Stemfie3D/STEMFIE-file-repository/Beams/Angled/U-shaped Symmetric/Beam AGD USH SYM ESS (thumbnail).png

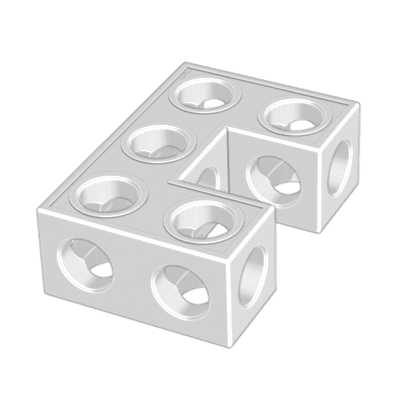
Beams/Angled/U-shaped Symmetric/Beam AGD USH SYM ESS (thumbnail).png
