Stemfie3D/STEMFIE-file-repository/Beams/Straight/Threaded Ends/Beam STR ERHRH DE ESS (thumbnail).png

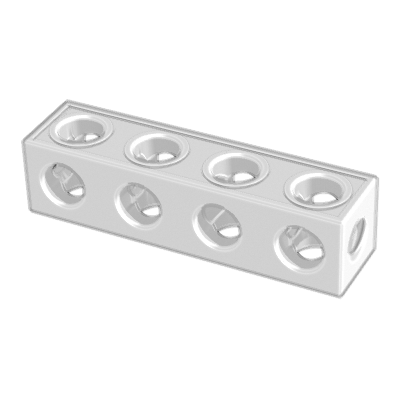
Beams/Straight/Threaded Ends/Beam STR ERHRH DE ESS (thumbnail).png
