Stemfie3D/STEMFIE-file-repository/Braces/Angled/90 Degrees Asymmetric/Brace AGD 90 ASYM ERR (thumbnail).png

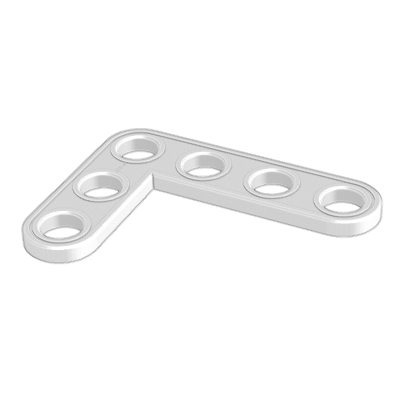
Braces/Angled/90 Degrees Asymmetric/Brace AGD 90 ASYM ERR (thumbnail).png
