Stemfie3D/STEMFIE-file-repository/Braces/Straight/Slotted Both Ends/Brace STR SLT BE SYM ERR (thumbnail).png

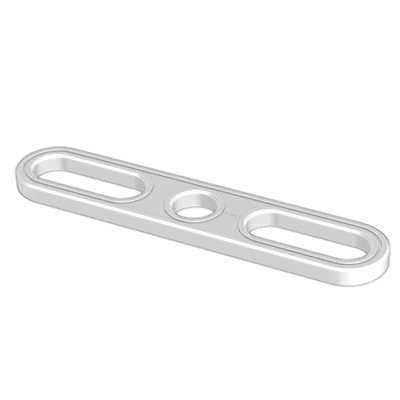
Braces/Straight/Slotted Both Ends/Brace STR SLT BE SYM ERR (thumbnail).png
