Stemfie3D/STEMFIE-file-repository/Braces/Straight/Slotted Sequential/Brace STR SLT SQT ERR (thumbnail).png

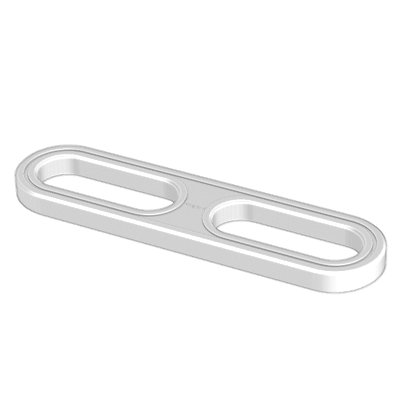
Braces/Straight/Slotted Sequential/Brace STR SLT SQT ERR (thumbnail).png
