Stemfie3D/STEMFIE-file-repository/Connectors/Beam Through-Hole/Connector BEM THR-H SFT (thumbnail).png

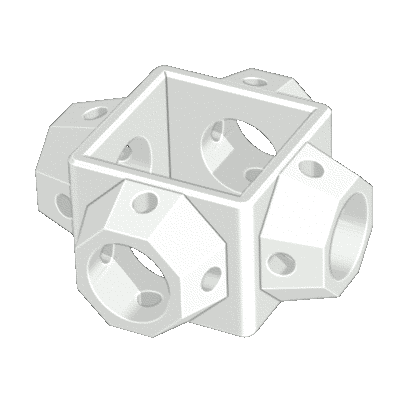
Connectors/Beam Through-Hole/Connector BEM THR-H SFT (thumbnail).png
