Stemfie3D/STEMFIE-file-repository/Fasteners/Nuts/Cam-locking/Open/Nut PH CL (thumbnail).png

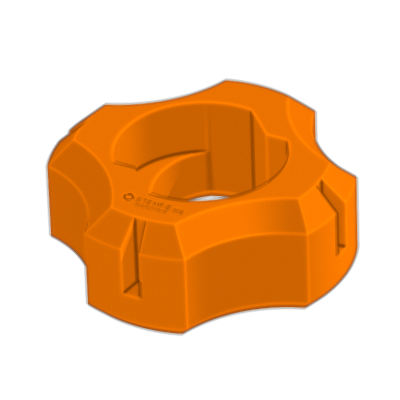
Fasteners/Nuts/Cam-locking/Open/Nut PH CL (thumbnail).png
