Stemfie3D/STEMFIE-file-repository/Fasteners/Nuts/Threaded/Open/Nut RH (thumbnail).png

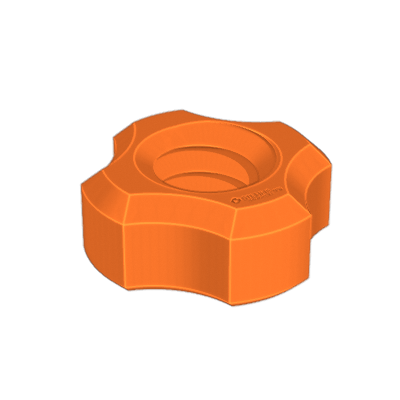
Fasteners/Nuts/Threaded/Open/Nut RH (thumbnail).png
