Stemfie3D/STEMFIE-file-repository/Fasteners/Screws/Fully Threaded STEMFIE Head/Screw SHD CRS STA FT RH (thumbnail).png

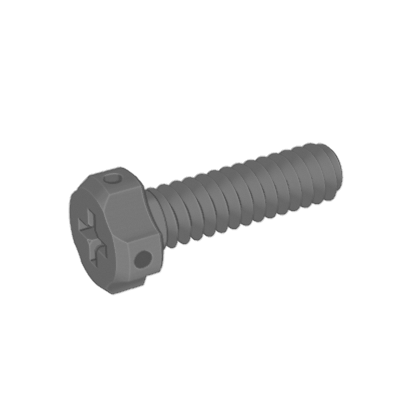
Fasteners/Screws/Fully Threaded STEMFIE Head/Screw SHD CRS STA FT RH (thumbnail).png
