Stemfie3D/STEMFIE-file-repository/Fasteners/Washers/Fixed/Washer FXD (thumbnail).png

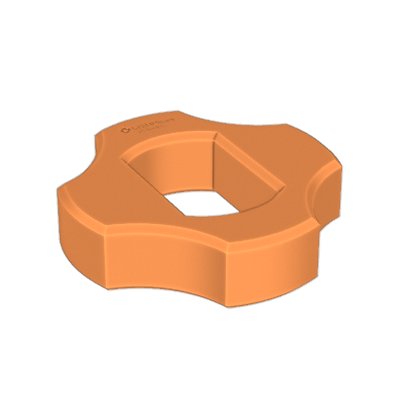
Fasteners/Washers/Fixed/Washer FXD (thumbnail).png
