Stemfie3D/STEMFIE-file-repository/Plates/3 - Triangular/Plate TRI (thumbnail).png

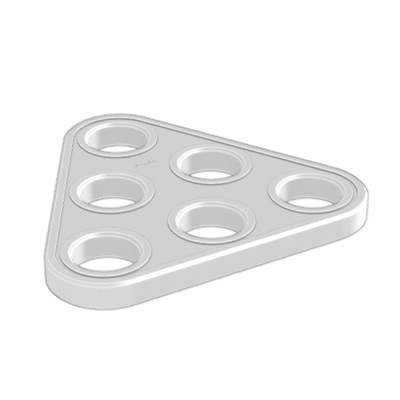
Plates/3 - Triangular/Plate TRI (thumbnail).png
