Stemfie3D/STEMFIE-file-repository/Plates/6 - Hexagonal/Plate HEX (thumbnail).png

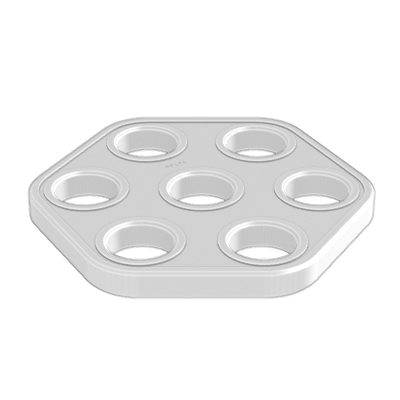
Plates/6 - Hexagonal/Plate HEX (thumbnail).png
