Stemfie3D/STEMFIE-file-repository/Springs/Rotor/Spring RTR (thumbnail).png

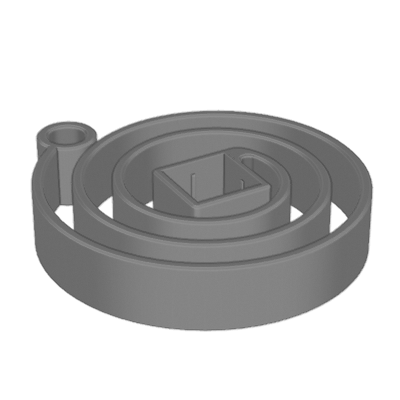
Springs/Rotor/Spring RTR (thumbnail).png
