Stemfie3D/STEMFIE-file-repository/Braces/Angled/90 Degrees Asymmetric/Brace AGD 90 ASYM ERR BU09x13x01x00.25 - SPN-BRC-1108 (stemfie.org).stl

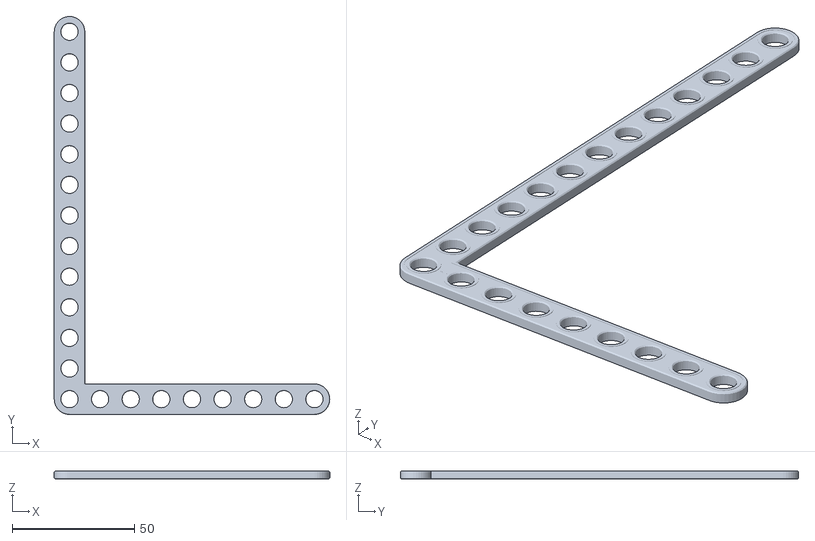
[picture p33: CAD file, 2023-08-30]
Braces/Angled/90 Degrees Asymmetric/Brace AGD 90 ASYM ERR BU09x13x01x00.25 - SPN-BRC-1108 (stemfie.org).stl
112.5 x 162.5 x 3.13
