Stemfie3D/STEMFIE-file-repository/Braces/Straight/Slotted Both Ends/Brace STR SLT BE SYM ERR BU20x01x00.25x09 - SPN-BRC-0372 (stemfie.org).stl

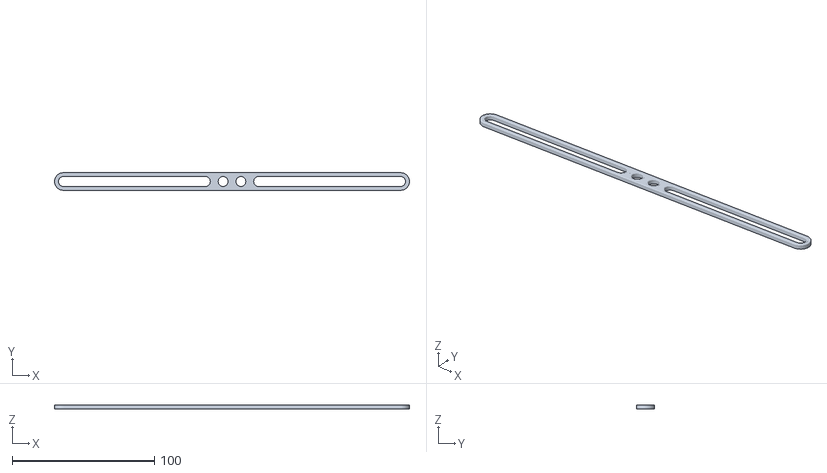
[picture p34: CAD file, 2021-05-27]
Braces/Straight/Slotted Both Ends/Brace STR SLT BE SYM ERR BU20x01x00.25x09 - SPN-BRC-0372 (stemfie.org).stl
250.0 x 12.5 x 3.13
