Stemfie3D/STEMFIE-file-repository/Braces/Straight/Slotted Centered/Brace STR SLT CNT ERR BU18x01x00.25x06 - SPN-BRC-0404 (stemfie.org).stl

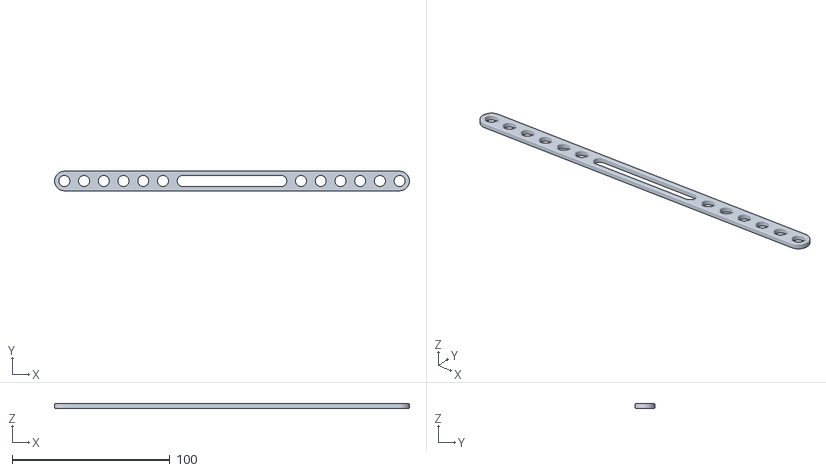
[picture p35: CAD file, 2021-05-27]
Braces/Straight/Slotted Centered/Brace STR SLT CNT ERR BU18x01x00.25x06 - SPN-BRC-0404 (stemfie.org).stl
225.0 x 12.5 x 3.12
