Stemfie3D/STEMFIE-file-repository/Braces/Straight/Slotted Full Length/Brace STR SLT FL ERR BU10x01x00.25 - SPN-BRC-0111 (stemfie.org).stl

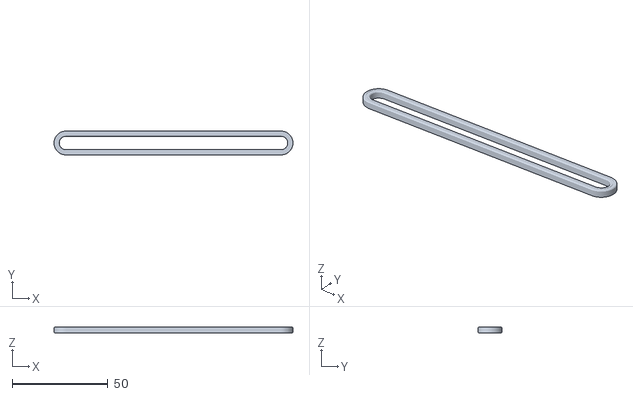
[picture p36: CAD file, 2021-05-27]
Braces/Straight/Slotted Full Length/Brace STR SLT FL ERR BU10x01x00.25 - SPN-BRC-0111 (stemfie.org).stl
125.0 x 12.5 x 3.13
