Stemfie3D/STEMFIE-file-repository/Braces/Straight/Slotted Sequential/Brace STR SLT SQT ERR BU04x01x00.25x02 - SPN-BRC-0419 (stemfie.org).stl

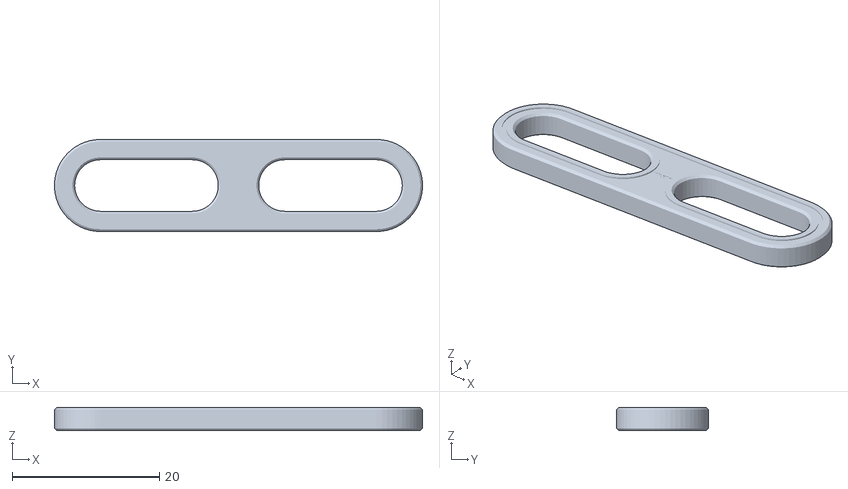
[picture p37: CAD file, 2022-02-20]
Braces/Straight/Slotted Sequential/Brace STR SLT SQT ERR BU04x01x00.25x02 - SPN-BRC-0419 (stemfie.org).stl
50.0 x 12.5 x 3.12
