Stemfie3D/STEMFIE-file-repository/Braces/Straight/Slotted Single End/Brace STR SLT SE ERR BU17x01x00.25x10 - SPN-BRC-0235 (stemfie.org).stl

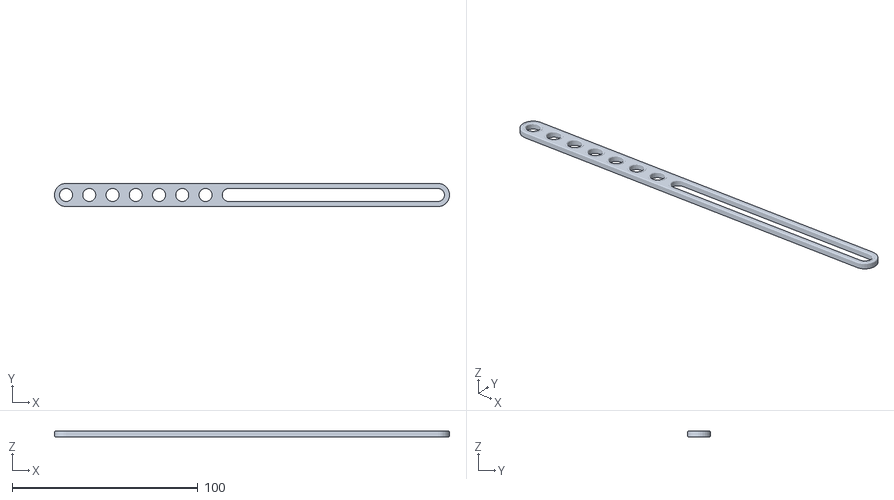
[picture p38: CAD file, 2021-05-27]
Braces/Straight/Slotted Single End/Brace STR SLT SE ERR BU17x01x00.25x10 - SPN-BRC-0235 (stemfie.org).stl
212.4 x 12.5 x 3.12
