Stemfie3D/STEMFIE-file-repository/Braces/Straight/Standard/Brace STR STD ERR BU27x01x00.25 - SPN-BRC-0026 (stemfie.org).stl

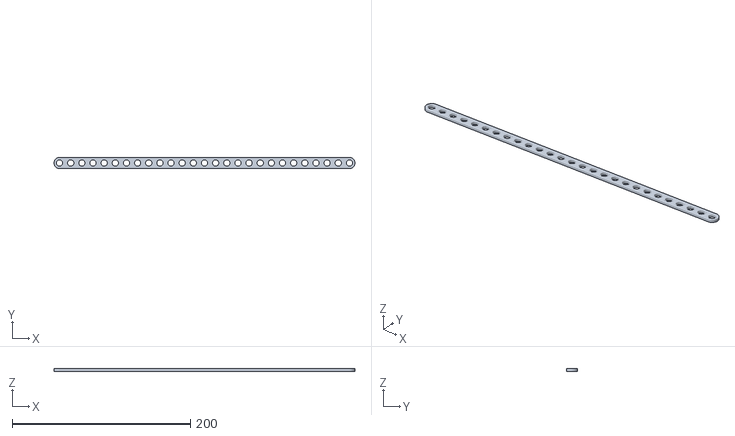
[picture p39: CAD file, 2021-05-27]
Braces/Straight/Standard/Brace STR STD ERR BU27x01x00.25 - SPN-BRC-0026 (stemfie.org).stl
337.5 x 12.5 x 3.12
