Stemfie3D/STEMFIE-file-repository/Braces/Straight/Standard/Build Plates/Brace STR ERR BU07x01x00.25 - SPN-BRC-0006 (stemfie.org) 13x 3D-printing build plate.3mf

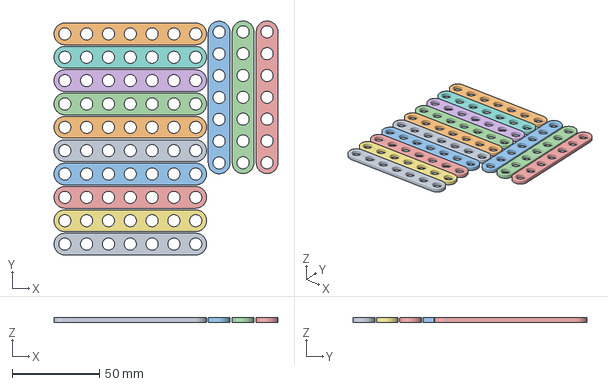
[picture p40: CAD file, 2021-05-27]
Braces/Straight/Standard/Build Plates/Brace STR ERR BU07x01x00.25 - SPN-BRC-0006 (stemfie.org) 13x 3D-printing build plate.3mf
128.3 x 134.1 x 3.12 mm
