Stemfie3D/STEMFIE-file-repository/Connectors/Beam Through-Hole/Connector BEM THR-H SFT 3W BU01x01x01x00.50 - SPN-CON-0004 (stemfie.org).stl

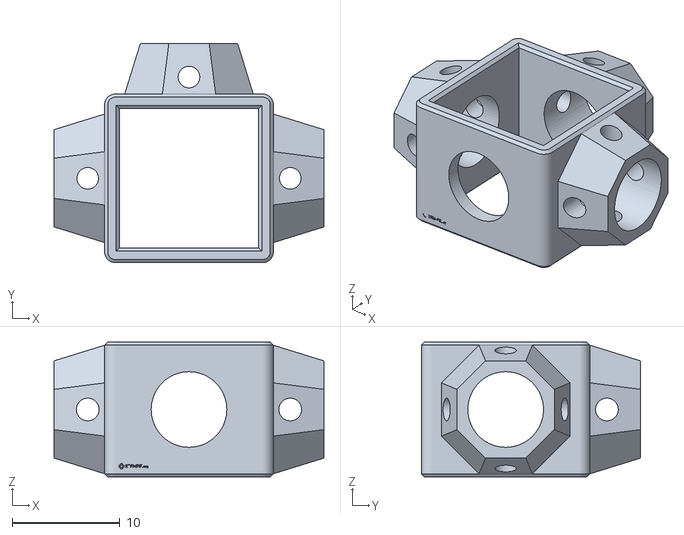
[picture p41: CAD file, 2021-05-27]
Connectors/Beam Through-Hole/Connector BEM THR-H SFT 3W BU01x01x01x00.50 - SPN-CON-0004 (stemfie.org).stl
25.0 x 20.3 x 12.5
