Stemfie3D/STEMFIE-file-repository/Holding Pulling Lifting/Spheres/Holder SPH LOP BRG-SCT INR-DIA BU02.50x02.00x01.50x01.25 - SPN-HLD-0007 (stemfie.org).stl

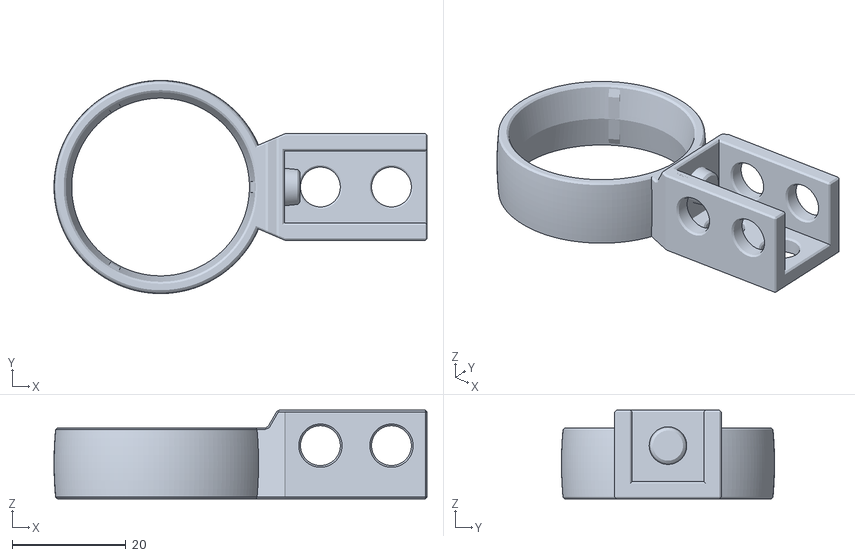
[picture p42: CAD file, 2021-10-22]
Holding Pulling Lifting/Spheres/Holder SPH LOP BRG-SCT INR-DIA BU02.50x02.00x01.50x01.25 - SPN-HLD-0007 (stemfie.org).stl
65.6 x 37.5 x 15.6
