Stemfie3D/STEMFIE-file-repository/Holding Pulling Lifting/Triggers/Holder Trigger BEM BU07x03x00.25 - SPN-HLD-0200 (stemfie.org).stl

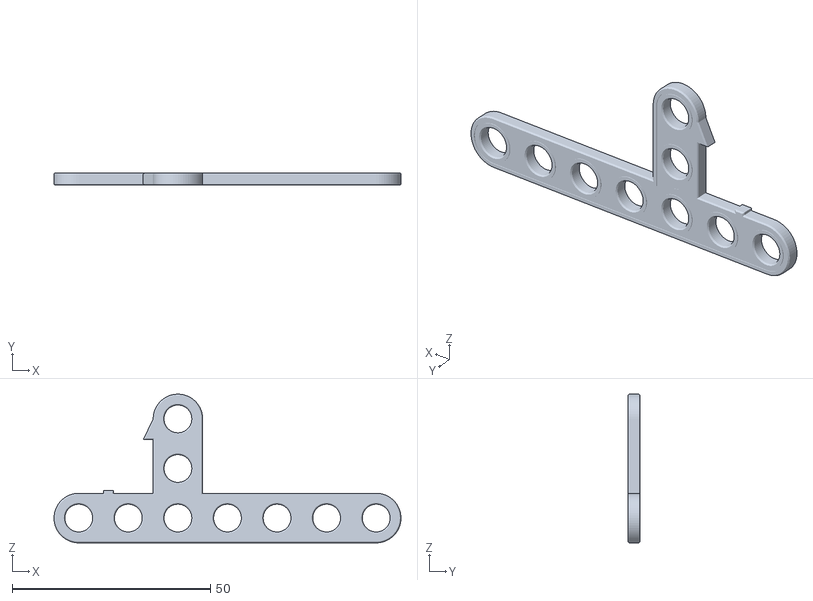
[picture p43: CAD file, 2021-10-22]
Holding Pulling Lifting/Triggers/Holder Trigger BEM BU07x03x00.25 - SPN-HLD-0200 (stemfie.org).stl
87.5 x 3.13 x 37.5
