Stemfie3D/STEMFIE-file-repository/Miscellaneous/Ornaments/Ornament Star - Five-Pointed (threaded) BU01x02x02 - SPN-ORN-0001 (stemfie.org) [with 3D-printing supports].stl

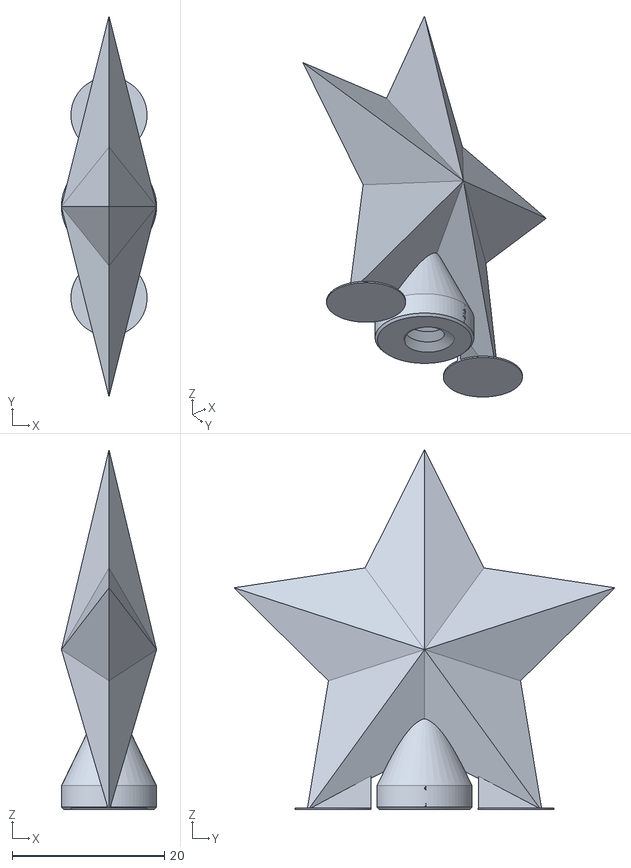
[picture p44: CAD file, 2021-05-27]
Miscellaneous/Ornaments/Ornament Star - Five-Pointed (threaded) BU01x02x02 - SPN-ORN-0001 (stemfie.org) [with 3D-printing supports].stl
12.5 x 50.0 x 47.3
