Stemfie3D/STEMFIE-file-repository/Miscellaneous/Signs/Build Plates/Sign URL THIN BU06x01x00.125 - SPN-SGN-0008 (stemfie.org) 20x 3D-printing build plate.3mf

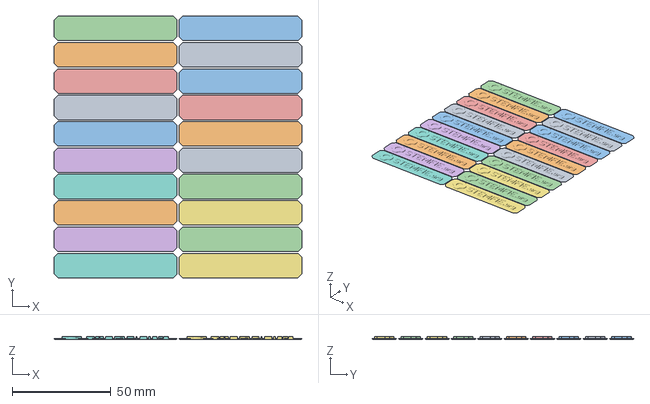
[picture p45: CAD file, 2021-05-27]
Miscellaneous/Signs/Build Plates/Sign URL THIN BU06x01x00.125 - SPN-SGN-0008 (stemfie.org) 20x 3D-printing build plate.3mf
125.9 x 132.9 x 1.56 mm
