Stemfie3D/STEMFIE-file-repository/Miscellaneous/Signs/Sign URL #OpenSource Plate HEX BU05x00.25 - SPN-SGN-0027 (stemfie.org).stl

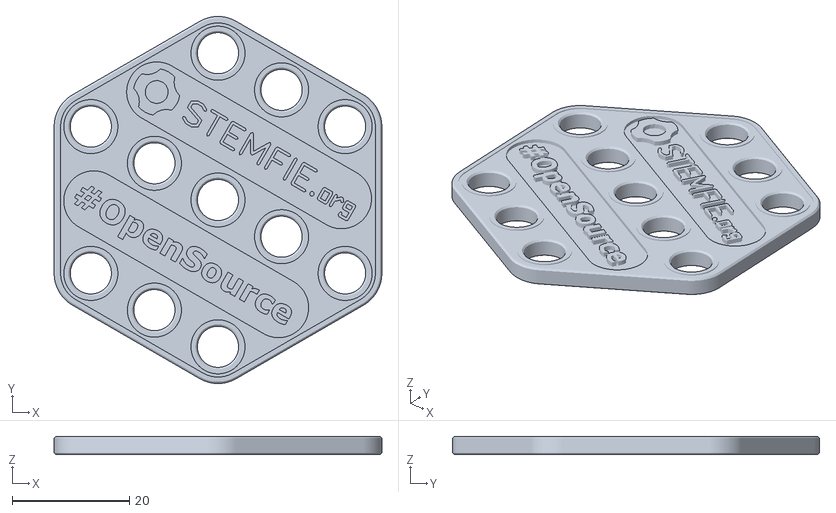
[picture p46: CAD file, 2023-04-05]
Miscellaneous/Signs/Sign URL #OpenSource Plate HEX BU05x00.25 - SPN-SGN-0027 (stemfie.org).stl
55.8 x 62.5 x 3.12
