Stemfie3D/STEMFIE-file-repository/Miscellaneous/Targets - Sights/Target Tipping BU05.25x03.00 - SPN-TRG-0001 (stemfie.org).stl

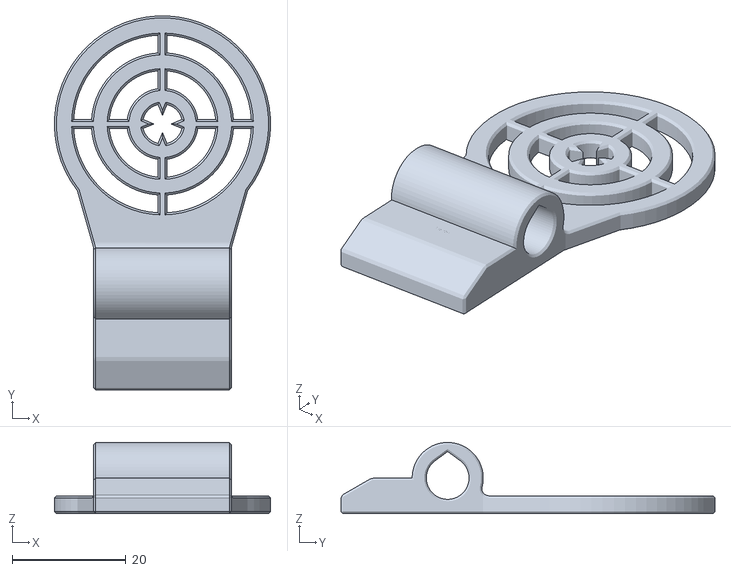
[picture p47: CAD file, 2021-10-22]
Miscellaneous/Targets - Sights/Target Tipping BU05.25x03.00 - SPN-TRG-0001 (stemfie.org).stl
38.0 x 65.7 x 12.5
