Stemfie3D/STEMFIE-file-repository/Non-printed/Ammunition/Nerf Dart Blunt 13 x 73 mm - SPN-NPH-0003/Nerf Dart Blunt 13 x 73 mm - SPN-NPH-0003 (stemfie.org).FCStd

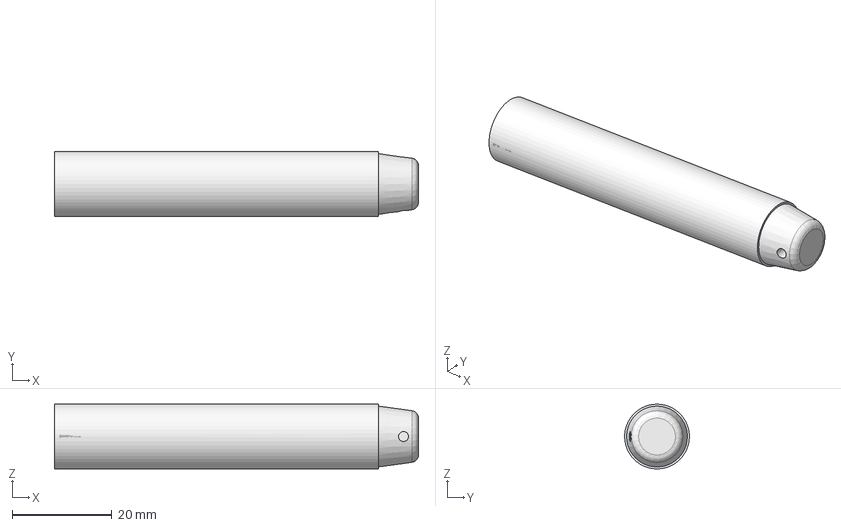
[picture p48: CAD file, 2023-04-06]
Non-printed/Ammunition/Nerf Dart Blunt 13 x 73 mm - SPN-NPH-0003/Nerf Dart Blunt 13 x 73 mm - SPN-NPH-0003 (stemfie.org).FCStd
73.0 x 13.0 x 13.0 mm
