Stemfie3D/STEMFIE-file-repository/Non-printed/Cutting/Blades/Single-Edge Razor Blade - SPN-NPH-0001/Single-Edge Razor Blade - SPN-NPH-0001 (stemfie.org).FCStd

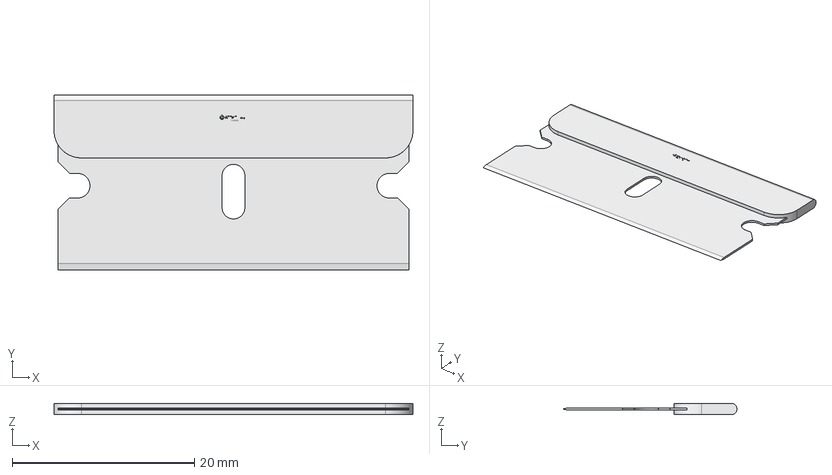
[picture p49: CAD file, 2023-04-06]
Non-printed/Cutting/Blades/Single-Edge Razor Blade - SPN-NPH-0001/Single-Edge Razor Blade - SPN-NPH-0001 (stemfie.org).FCStd
39.4 x 19.2 x 1.25 mm
