Stemfie3D/STEMFIE-file-repository/Non-printed/Spherical/Ping-Pong ball - 40 mm 2.7 grams - SPN-NPH-0004/Ping-Pong ball - 40 mm 2.7 grams - SPN-NPH-0004 (stemfie.org).FCStd

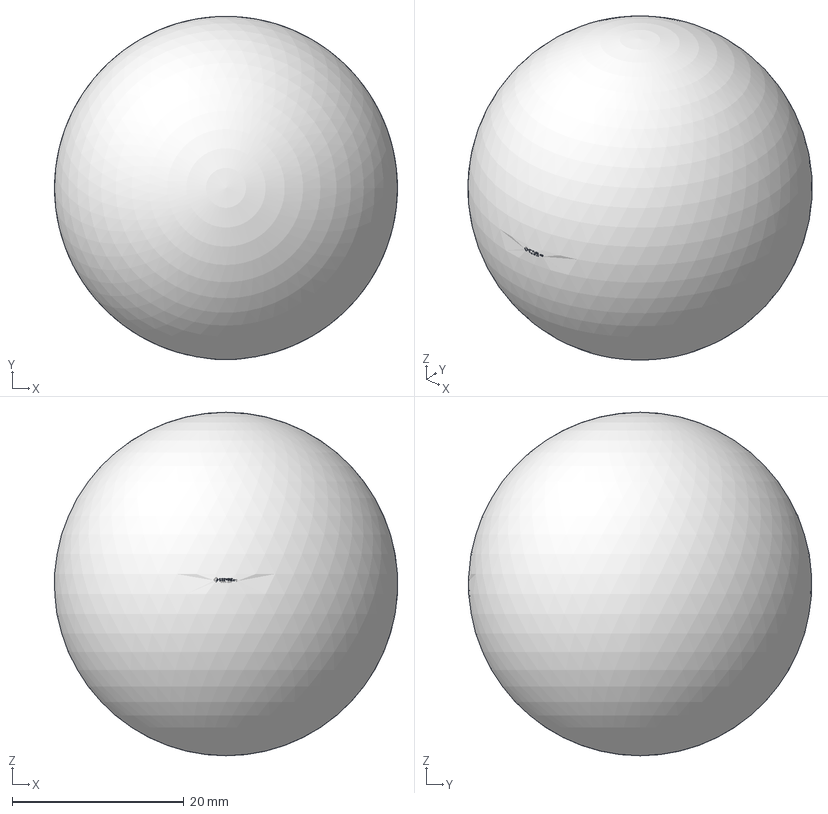
[picture p50: CAD file, 2023-04-06]
Non-printed/Spherical/Ping-Pong ball - 40 mm 2.7 grams - SPN-NPH-0004/Ping-Pong ball - 40 mm 2.7 grams - SPN-NPH-0004 (stemfie.org).FCStd
39.9 x 40.0 x 40.0 mm
