Stemfie3D/STEMFIE-file-repository/Plates/3 - Triangular/Plate TRI BU11x00.25 - SPN-PLT-0022 (stemfie.org).stl

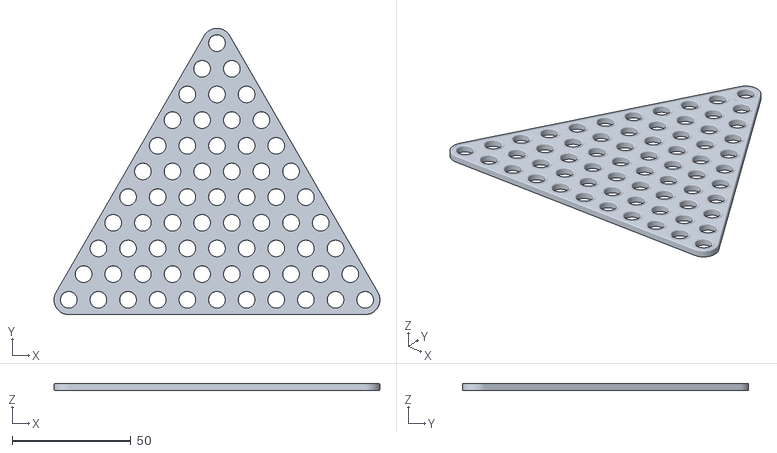
[picture p51: CAD file, 2023-01-02]
Plates/3 - Triangular/Plate TRI BU11x00.25 - SPN-PLT-0022 (stemfie.org).stl
137.5 x 120.8 x 3.13
