Stemfie3D/STEMFIE-file-repository/Plates/4 - Square/Plate SQR BU04x00.25 - SPN-PLT-0039 (stemfie.org).stl

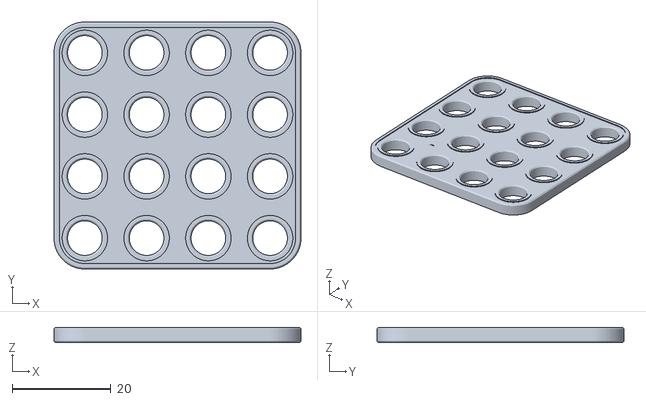
[picture p52: CAD file, 2023-01-02]
Plates/4 - Square/Plate SQR BU04x00.25 - SPN-PLT-0039 (stemfie.org).stl
50.0 x 50.0 x 3.13
