Stemfie3D/STEMFIE-file-repository/Plates/6 - Hexagonal/Plate HEX BU03x00.25 - SPN-PLT-0001 (stemfie.org).stl

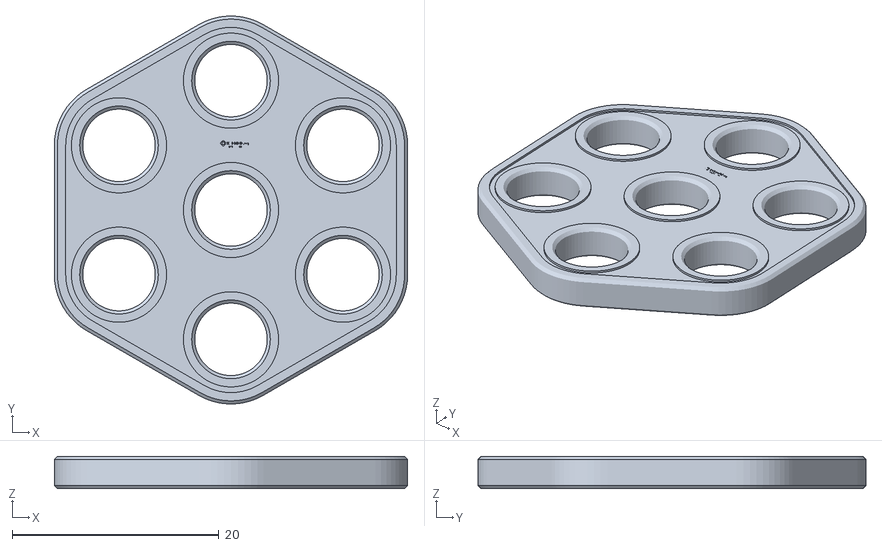
[picture p53: CAD file, 2023-01-02]
Plates/6 - Hexagonal/Plate HEX BU03x00.25 - SPN-PLT-0001 (stemfie.org).stl
34.2 x 37.5 x 3.13
