Stemfie3D/STEMFIE-file-repository/Power Transmission/Motors/N20 Geared Motor (WIP)/N20 Geared Motor.FCStd

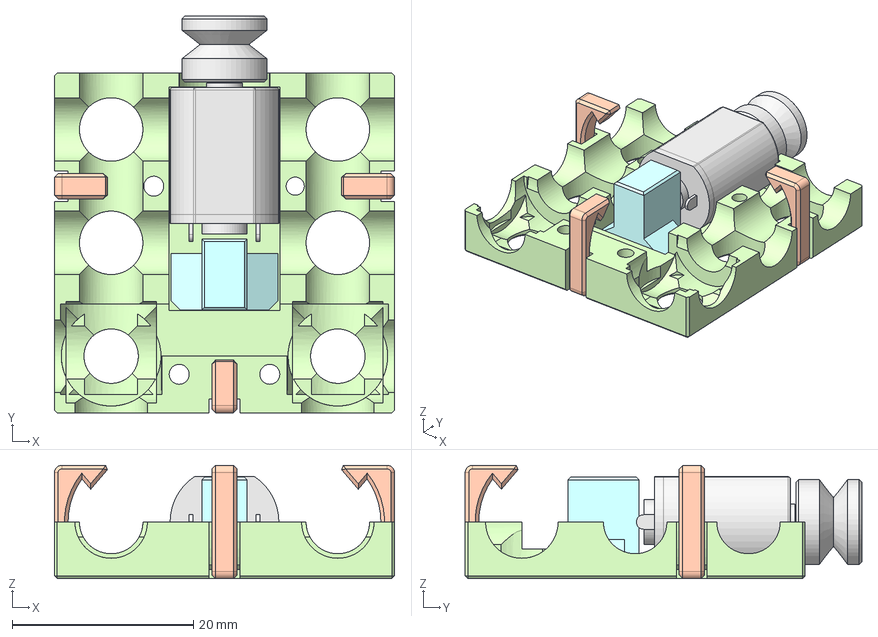
[picture p54: CAD file, 2022-03-13]
Power Transmission/Motors/N20 Geared Motor (WIP)/N20 Geared Motor.FCStd
37.5 x 43.8 x 12.5 mm
Clamp x 3
Motor
Standoff for ungearned N20
Pulley
