Stemfie3D/STEMFIE-file-repository/Power Transmission/Pulleys/Wheel Pulley FXD BRD THREYE BU01.00x01.00 - SPN-WHL0005 (stemfie.org).stl

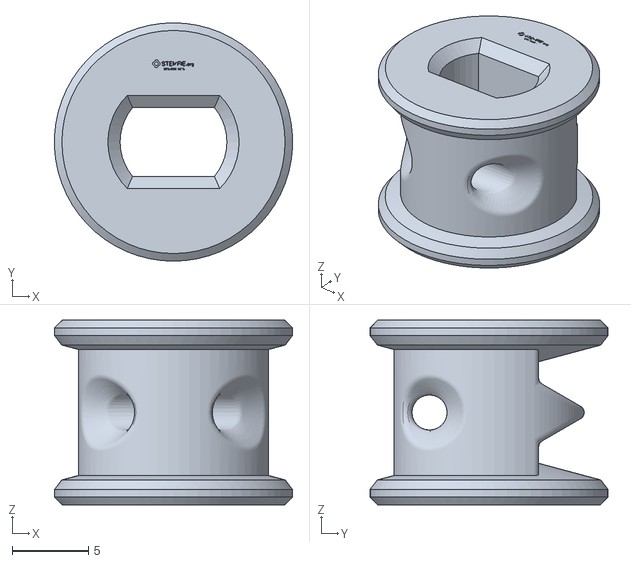
[picture p55: CAD file, 2021-05-27]
Power Transmission/Pulleys/Wheel Pulley FXD BRD THREYE BU01.00x01.00 - SPN-WHL0005 (stemfie.org).stl
15.6 x 15.6 x 12.1
