Stemfie3D/STEMFIE-file-repository/Power Transmission/Wheels/Ground/Wheel GND TTRD FXD BU03.00x01.00 - SPN-WHL-0002 (stemfie.org).stl

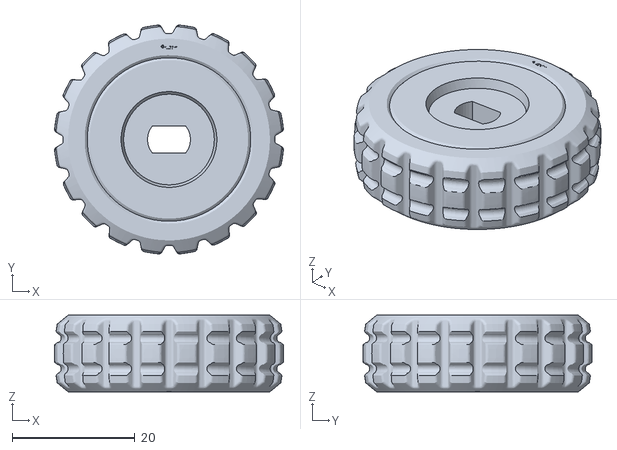
[picture p56: CAD file, 2021-05-27]
Power Transmission/Wheels/Ground/Wheel GND TTRD FXD BU03.00x01.00 - SPN-WHL-0002 (stemfie.org).stl
37.4 x 37.4 x 12.5
