Stemfie3D/STEMFIE-file-repository/Projects/SPS-000001 - Rubber-band-driven car/Build plates/SPS-000001 - Rubber-band-driven car - Instruction URL (stemfie.org).stl

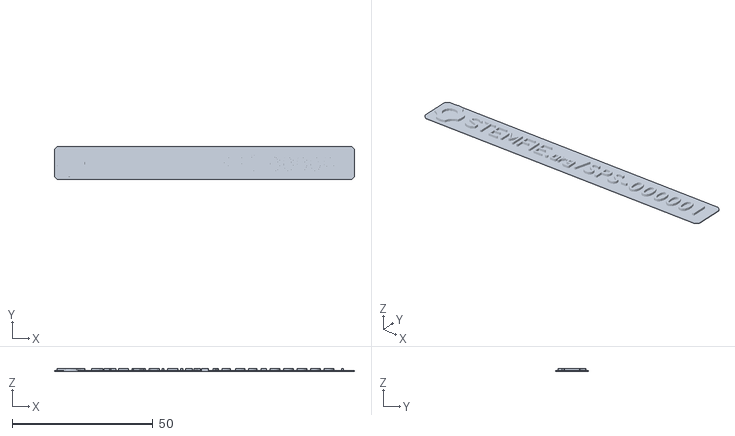
[picture p57: CAD file, 2023-01-02]
Projects/SPS-000001 - Rubber-band-driven car/Build plates/SPS-000001 - Rubber-band-driven car - Instruction URL (stemfie.org).stl
106.7 x 11.8 x 1.20
