Stemfie3D/STEMFIE-file-repository/Projects/SPS-000002 - Desktop Christmas Tree/Build Plates/SPS-000002 - Desktop Christmas Tree - Nuts - Coloured (stemfie.org).3mf

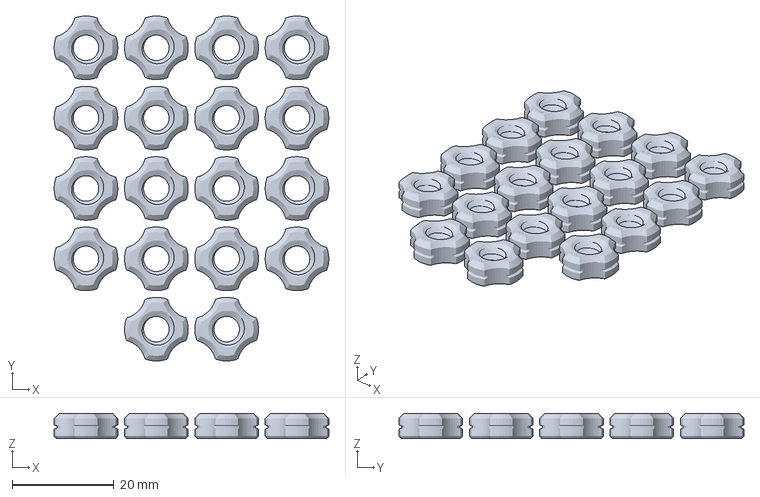
[picture p58: CAD file, 2022-02-20]
Projects/SPS-000002 - Desktop Christmas Tree/Build Plates/SPS-000002 - Desktop Christmas Tree - Nuts - Coloured (stemfie.org).3mf
53.9 x 67.7 x 5.00 mm
