Stemfie3D/STEMFIE-file-repository/Shafts/Plain/Shaft PLN BU01.50 - SPN-SFT-0006 (stemfie.org).stl

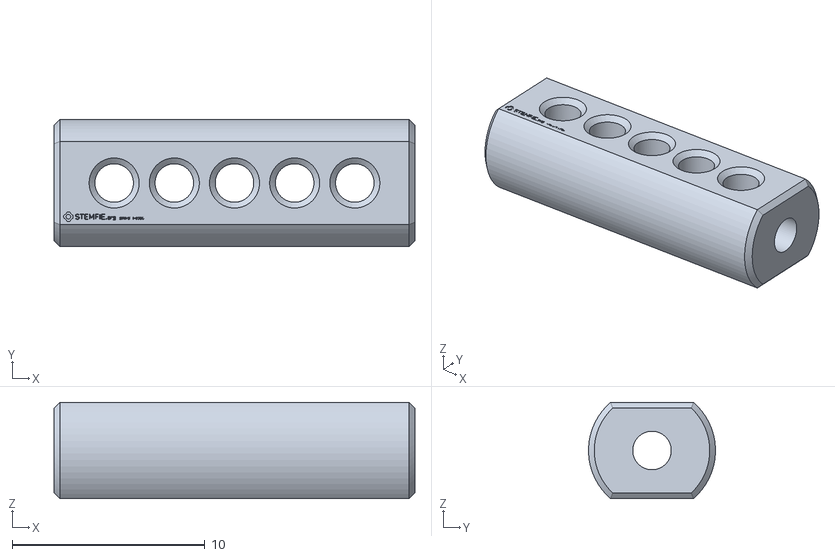
[picture p59: CAD file, 2023-08-03]
Shafts/Plain/Shaft PLN BU01.50 - SPN-SFT-0006 (stemfie.org).stl
18.8 x 6.59 x 5.00
