Stemfie3D/STEMFIE-file-repository/Springs/Rotor/Spring RTR BU05.00x01.00 E-BU01.00x01.00-BUH REV2.5 T2mm - SPN-SPG-0005 (stemfie.org).stl

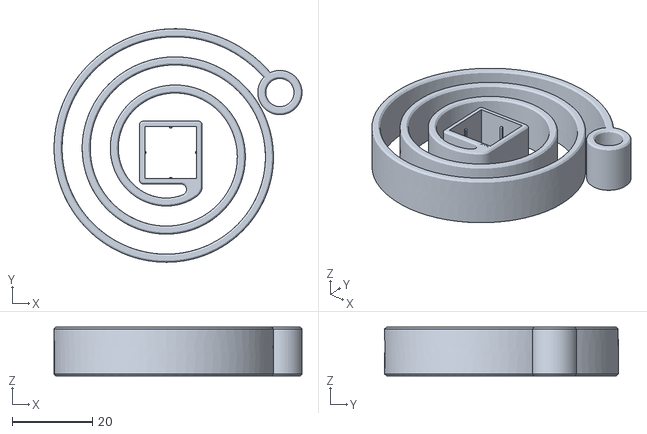
[picture p60: CAD file, 2021-10-22]
Springs/Rotor/Spring RTR BU05.00x01.00 E-BU01.00x01.00-BUH REV2.5 T2mm - SPN-SPG-0005 (stemfie.org).stl
61.6 x 58.0 x 12.1
