Stemfie3D/STEMFIE-file-repository/Templates/FreeCAD/STEMFIE.org_FreeCAD_template_scene.FCStd

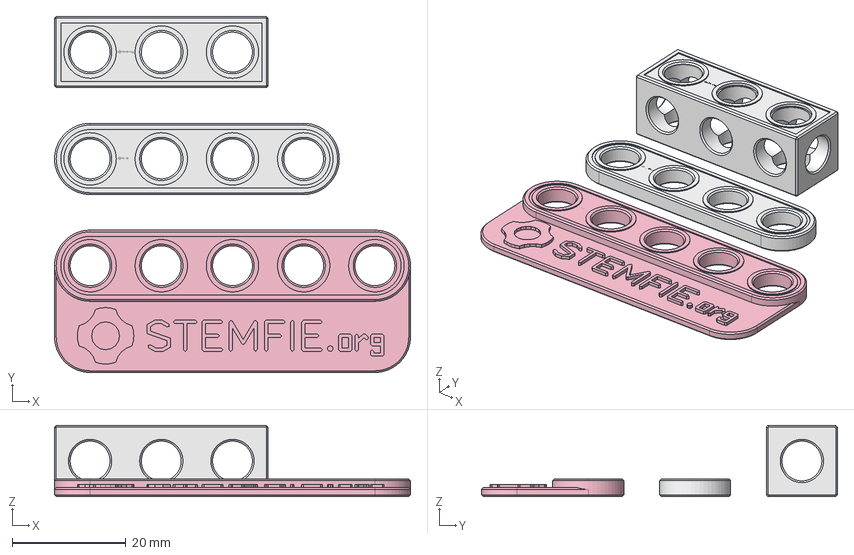
[picture p61: CAD file, 2023-06-29]
Templates/FreeCAD/STEMFIE.org_FreeCAD_template_scene.FCStd
62.5 x 62.5 x 12.5 mm
Beam STR ESS (stemfie.org)
Brace STR ERR (stemfie.org)
Sign URL BEM BU04x02x00.25 - SPN-SGN-0006 (stemfie.org)001
