Stemfie3D/STEMFIE-file-repository/Templates/STEMFIE Construction Standard/STEMFIE Construction Standard - Template - Block Unit BU01x01x01 - SCS-TPL-0001 (stemfie.org).stl

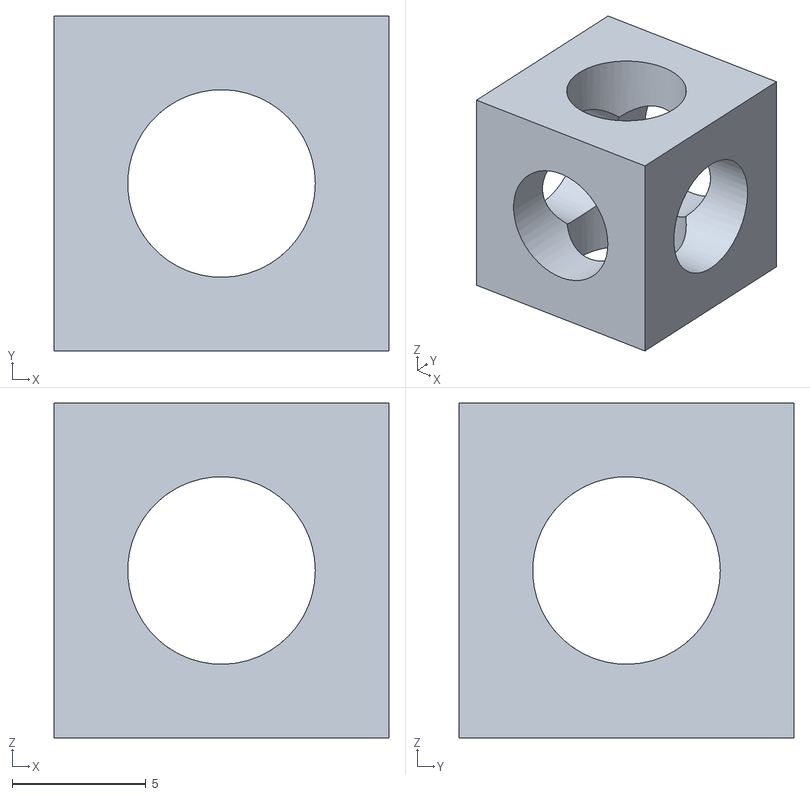
[picture p62: CAD file, 2022-02-03]
Templates/STEMFIE Construction Standard/STEMFIE Construction Standard - Template - Block Unit BU01x01x01 - SCS-TPL-0001 (stemfie.org).stl
12.5 x 12.5 x 12.5
