Stemfie3D/STEMFIE-file-repository/Tools/Storage/Parts Drawer/Parts Storage Drawer Section Divider LNG BU10.00x03.75 - SPN-TOL-0052 (stemfie.org).stl

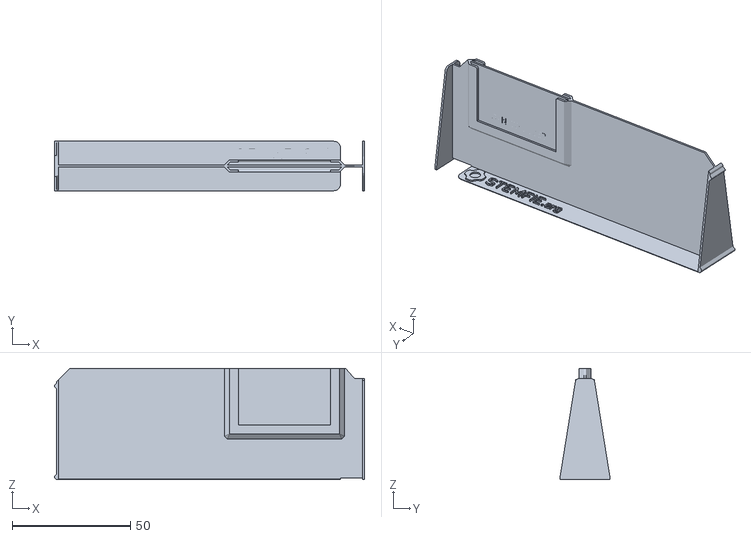
[picture p63: CAD file, 2023-03-22]
Tools/Storage/Parts Drawer/Parts Storage Drawer Section Divider LNG BU10.00x03.75 - SPN-TOL-0052 (stemfie.org).stl
131.3 x 21.0 x 47.2
