Stemfie3D/STEMFIE-file-repository/Beams/Angled/T-shaped Symmetric/Beam AGD TSH SYM ESS BU13x15x01 - SPN-BEM-1108 (stemfie.org).stl

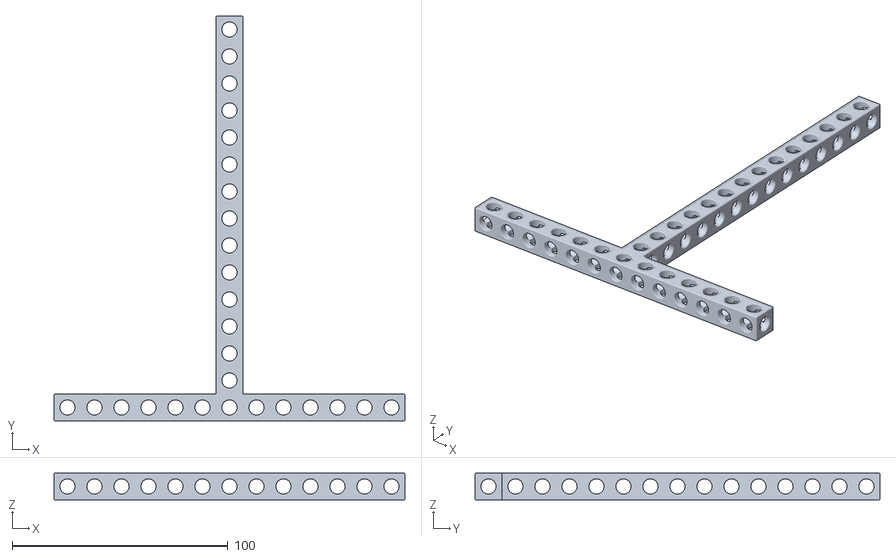
[picture p64: CAD file, 2022-01-30]
Beams/Angled/T-shaped Symmetric/Beam AGD TSH SYM ESS BU13x15x01 - SPN-BEM-1108 (stemfie.org).stl
162.5 x 187.5 x 12.5
