Stemfie3D/STEMFIE-file-repository/Beams/Angled/T-shaped Symmetric/Build Plates/Beam AGD TSH SYM ESS BU05x17x01 - SPN-BEM-1034 (stemfie.org) 8x 3D-printing build plate.3mf

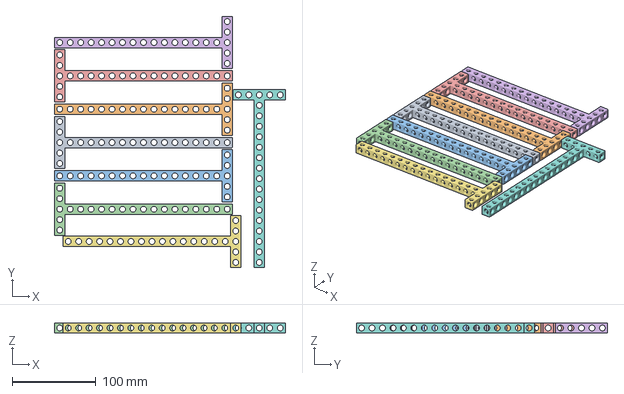
[picture p65: CAD file, 2022-04-08]
Beams/Angled/T-shaped Symmetric/Build Plates/Beam AGD TSH SYM ESS BU05x17x01 - SPN-BEM-1034 (stemfie.org) 8x 3D-printing build plate.3mf
275.8 x 300.0 x 12.5 mm
