Stemfie3D/STEMFIE-file-repository/Beams/Angled/U-shaped Symmetric/Beam AGD USH SYM ESS BU16x18x01 - SPN-BEM-0572 (stemfie.org).stl

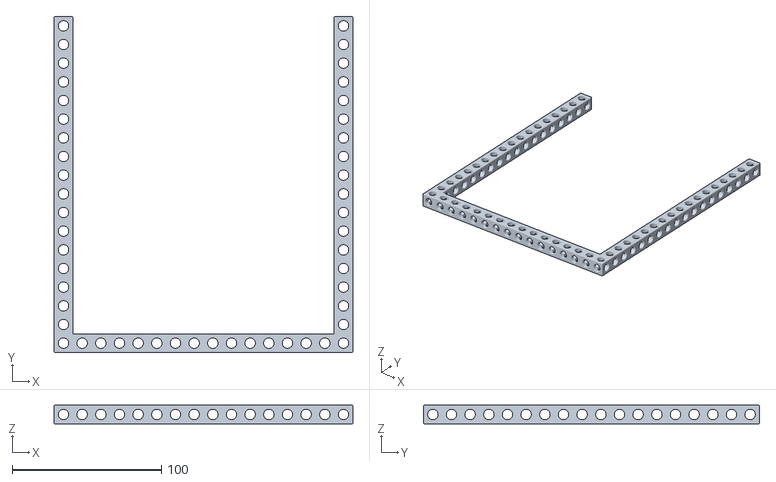
[picture p66: CAD file, 2022-04-05]
Beams/Angled/U-shaped Symmetric/Beam AGD USH SYM ESS BU16x18x01 - SPN-BEM-0572 (stemfie.org).stl
200.0 x 225.0 x 12.5
