Stemfie3D/STEMFIE-file-repository/Beams/Angled/U-shaped Symmetric/Build Plates/Beam AGD USH SYM ESS BU05x15x01 - SPN-BEM-0352 (stemfie.org) 3x 3D Printing Build Plate.3mf

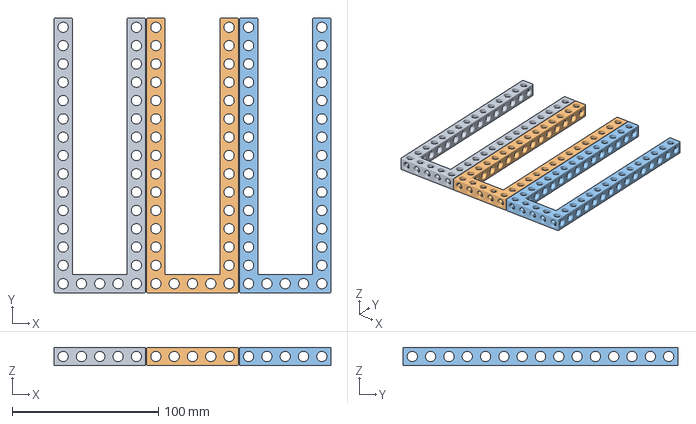
[picture p67: CAD file, 2023-02-07]
Beams/Angled/U-shaped Symmetric/Build Plates/Beam AGD USH SYM ESS BU05x15x01 - SPN-BEM-0352 (stemfie.org) 3x 3D Printing Build Plate.3mf
189.1 x 187.5 x 12.5 mm
