Stemfie3D/STEMFIE-file-repository/Beams/Straight/Box-section/Beam STR BXS ESS BU09.00x01.00x01.00x01.00x00.125 - SPN-BEM-0406 (stemfie.org).stl

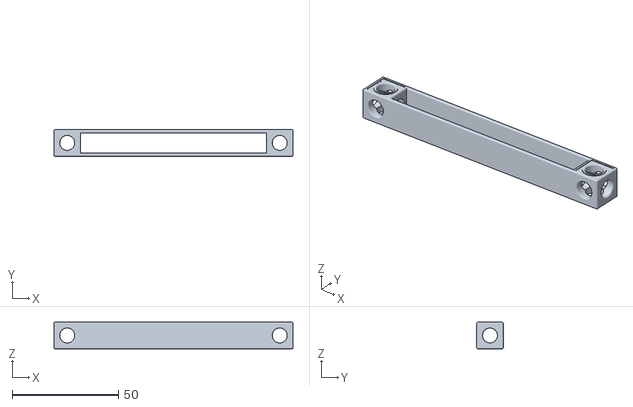
[picture p68: CAD file, 2021-05-27]
Beams/Straight/Box-section/Beam STR BXS ESS BU09.00x01.00x01.00x01.00x00.125 - SPN-BEM-0406 (stemfie.org).stl
112.5 x 12.5 x 12.5
