Stemfie3D/STEMFIE-file-repository/Beams/Straight/Box-section/Build Plates/Beam STR BXS ESS BU01.50x01.00x01.00x00.25x00.125 - SPN-BEM-0003 (stemfie.org) 70x 3D-printing build plate.3mf

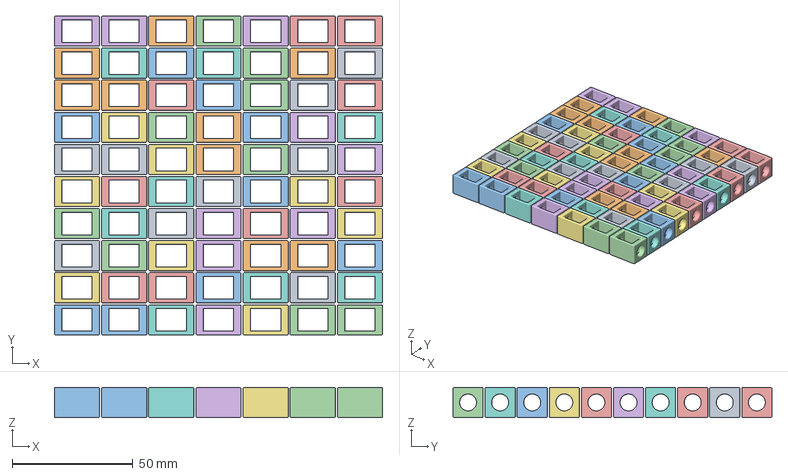
[picture p69: CAD file, 2022-04-08]
Beams/Straight/Box-section/Build Plates/Beam STR BXS ESS BU01.50x01.00x01.00x00.25x00.125 - SPN-BEM-0003 (stemfie.org) 70x 3D-printing build plate.3mf
136.1 x 132.2 x 12.5 mm
