Stemfie3D/STEMFIE-file-repository/Beams/Straight/Square Ends/Beam STR ESS BU12x01x01 - SPN-BEM-0049 (stemfie.org).stl

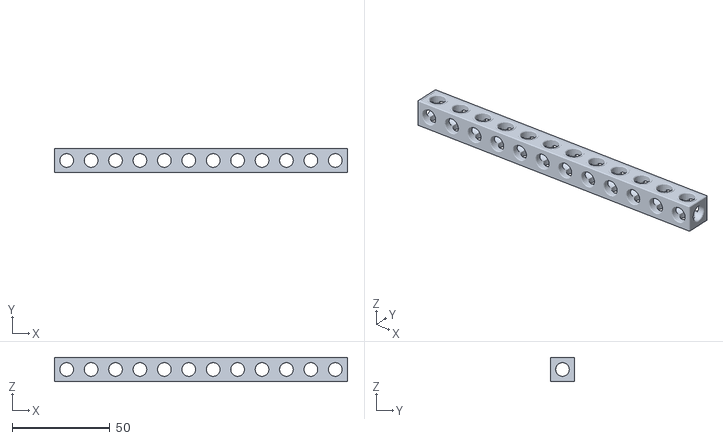
[picture p70: CAD file, 2021-05-30]
Beams/Straight/Square Ends/Beam STR ESS BU12x01x01 - SPN-BEM-0049 (stemfie.org).stl
150.0 x 12.5 x 12.5
