Stemfie3D/STEMFIE-file-repository/Beams/Straight/Square Ends/Build Plates/Beam STR ESS BU38x01x01 - SPN-BEM-0075 (stemfie.org) 68x 3D-printing build plate.3mf

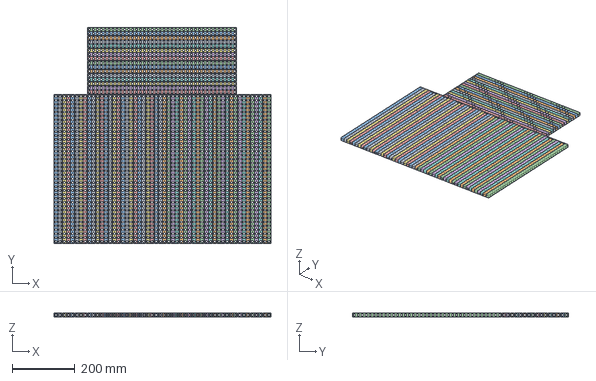
[picture p71: CAD file, 2022-04-08]
Beams/Straight/Square Ends/Build Plates/Beam STR ESS BU38x01x01 - SPN-BEM-0075 (stemfie.org) 68x 3D-printing build plate.3mf
690.8 x 687.8 x 12.5 mm
