Stemfie3D/STEMFIE-file-repository/Beams/Straight/Threaded Ends/Beam STR ERHRH DE ESS BU13x01x01 - SPN-BEM-0812 (stemfie.org).stl

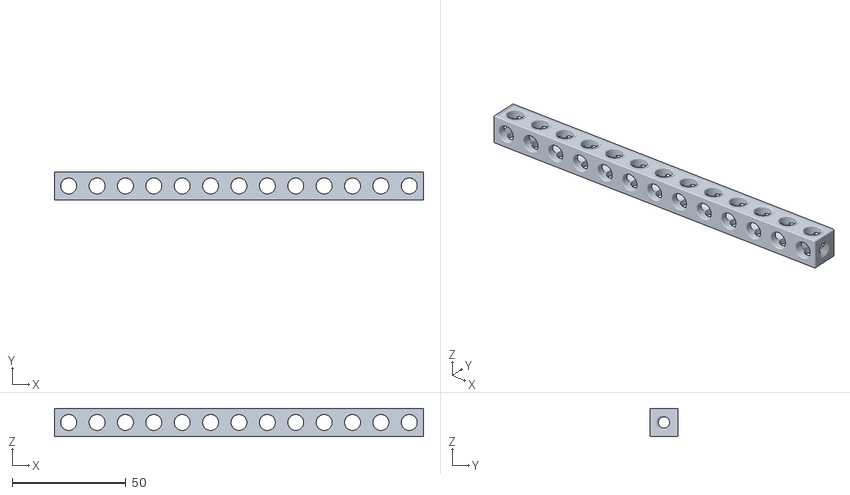
[picture p72: CAD file, 2021-07-01]
Beams/Straight/Threaded Ends/Beam STR ERHRH DE ESS BU13x01x01 - SPN-BEM-0812 (stemfie.org).stl
162.5 x 12.5 x 12.5
