Stemfie3D/STEMFIE-file-repository/Braces/Angled/90 Degrees Asymmetric/Brace AGD 90 ASYM ERR BU10x11x01x00.25 - SPN-BRC-1116 (stemfie.org).stl

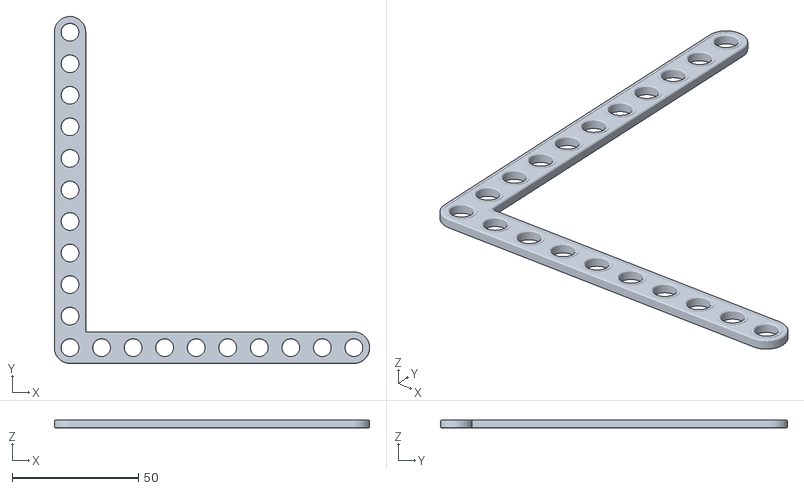
[picture p74: CAD file, 2023-08-30]
Braces/Angled/90 Degrees Asymmetric/Brace AGD 90 ASYM ERR BU10x11x01x00.25 - SPN-BRC-1116 (stemfie.org).stl
125.0 x 137.5 x 3.13
