Stemfie3D/STEMFIE-file-repository/Braces/Straight/Slotted Both Ends/Brace STR SLT BE SYM ERR BU14x01x00.25x05 - SPN-BRC-0326 (stemfie.org).stl

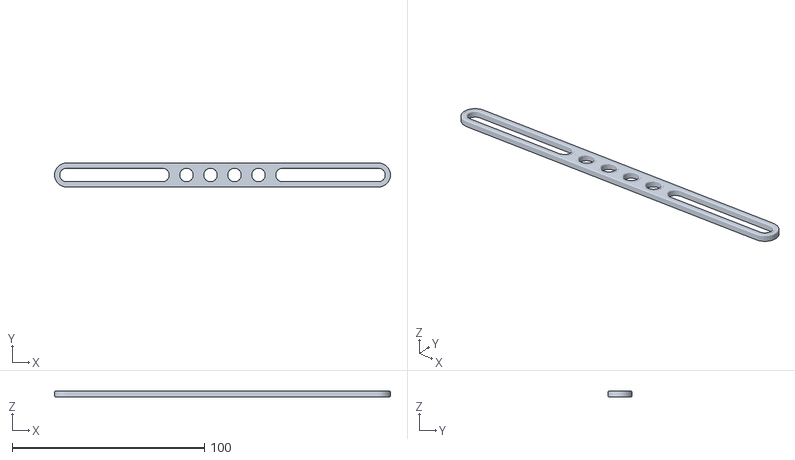
[picture p75: CAD file, 2021-05-27]
Braces/Straight/Slotted Both Ends/Brace STR SLT BE SYM ERR BU14x01x00.25x05 - SPN-BRC-0326 (stemfie.org).stl
175.0 x 12.5 x 3.12
