Stemfie3D/STEMFIE-file-repository/Braces/Straight/Slotted Centered/Brace STR SLT CNT ERR BU08x01x00.25x06 - SPN-BRC-0379 (stemfie.org).stl

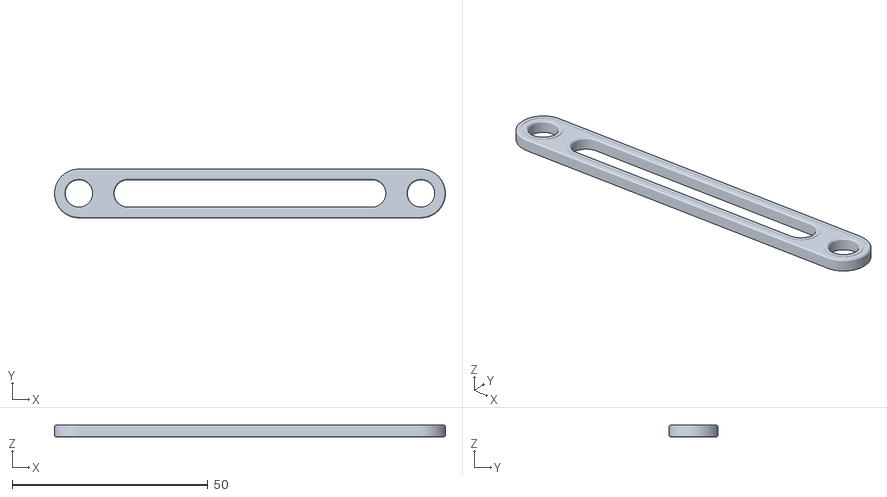
[picture p76: CAD file, 2021-05-27]
Braces/Straight/Slotted Centered/Brace STR SLT CNT ERR BU08x01x00.25x06 - SPN-BRC-0379 (stemfie.org).stl
100.0 x 12.5 x 3.13
