Stemfie3D/STEMFIE-file-repository/Braces/Straight/Slotted Full Length/Brace STR SLT FL ERR BU04x01x00.25 - SPN-BRC-0105 (stemfie.org).stl

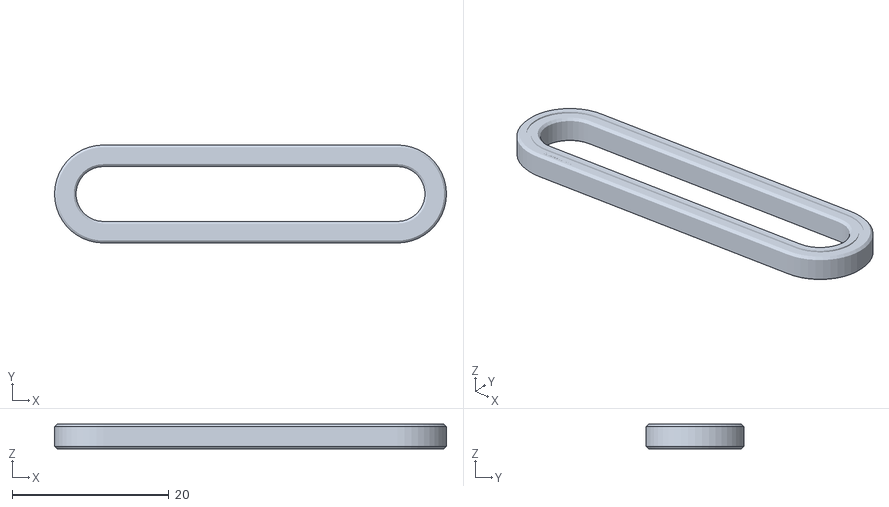
[picture p77: CAD file, 2021-05-27]
Braces/Straight/Slotted Full Length/Brace STR SLT FL ERR BU04x01x00.25 - SPN-BRC-0105 (stemfie.org).stl
50.0 x 12.5 x 3.13
