Stemfie3D/STEMFIE-file-repository/Braces/Straight/Slotted Sequential/Brace STR SLT SQT ERR BU14x01x00.25x07 - SPN-BRC-0431 (stemfie.org).stl

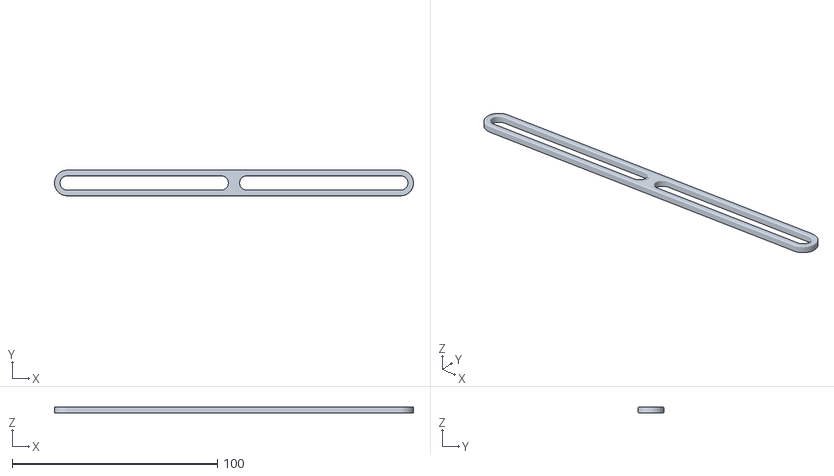
[picture p78: CAD file, 2022-02-20]
Braces/Straight/Slotted Sequential/Brace STR SLT SQT ERR BU14x01x00.25x07 - SPN-BRC-0431 (stemfie.org).stl
175.0 x 12.5 x 3.12
