Stemfie3D/STEMFIE-file-repository/Braces/Straight/Slotted Single End/Brace STR SLT SE ERR BU15x01x00.25x03 - SPN-BRC-0201 (stemfie.org).stl

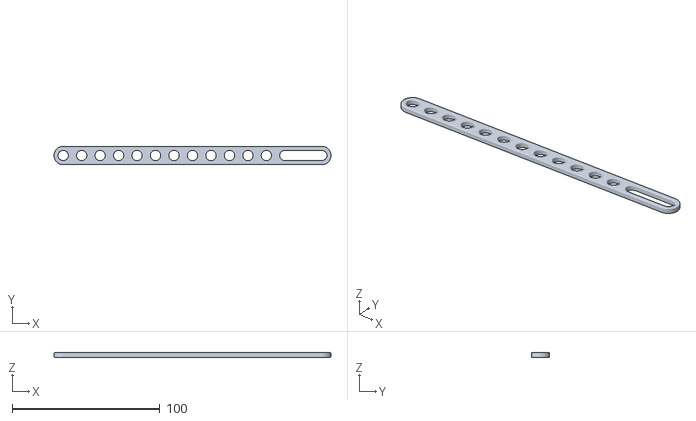
[picture p79: CAD file, 2021-05-27]
Braces/Straight/Slotted Single End/Brace STR SLT SE ERR BU15x01x00.25x03 - SPN-BRC-0201 (stemfie.org).stl
187.5 x 12.5 x 3.12
