Stemfie3D/STEMFIE-file-repository/Braces/Straight/Standard/Brace STR STD ERR BU38x01x00.25 - SPN-BRC-0037 (stemfie.org).stl

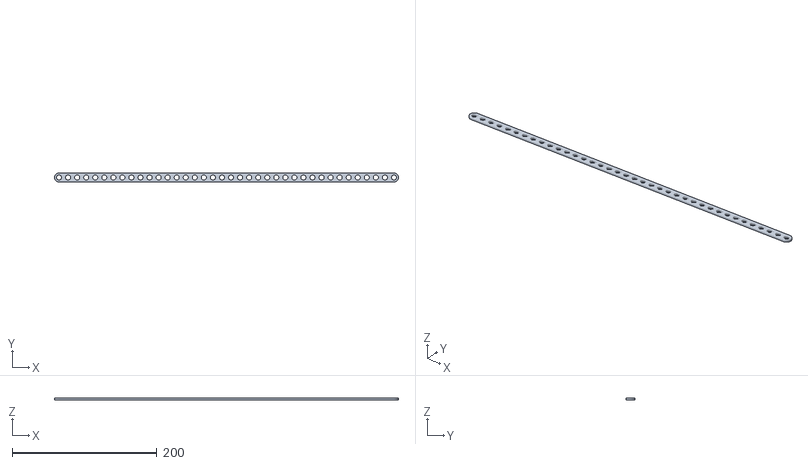
[picture p80: CAD file, 2021-05-27]
Braces/Straight/Standard/Brace STR STD ERR BU38x01x00.25 - SPN-BRC-0037 (stemfie.org).stl
475.0 x 12.5 x 3.12
