Stemfie3D/STEMFIE-file-repository/Braces/Straight/Standard/Build Plates/Brace STR ERR BU03x01x00.25 - SPN-BRC-0002 (stemfie.org) 36x 3D-printing build plate.3mf

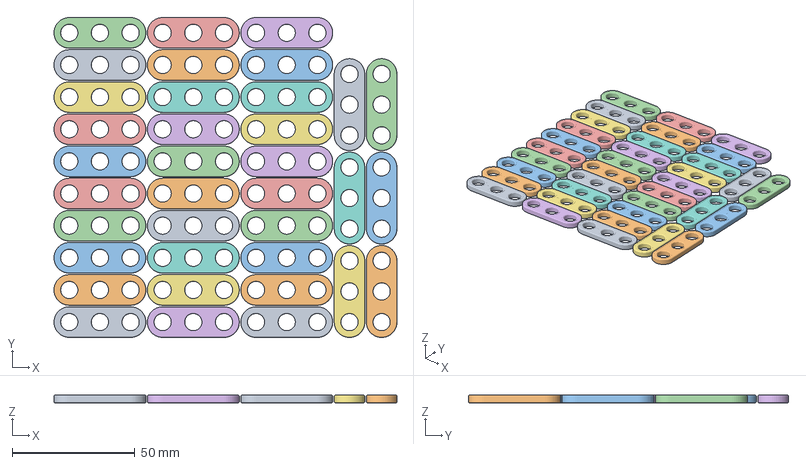
[picture p81: CAD file, 2021-05-27]
Braces/Straight/Standard/Build Plates/Brace STR ERR BU03x01x00.25 - SPN-BRC-0002 (stemfie.org) 36x 3D-printing build plate.3mf
139.8 x 130.4 x 3.12 mm
