Stemfie3D/STEMFIE-file-repository/Connectors/Beam Through-Hole/Connector BEM THR-H SFT 4W BU01x01x01x00.50 - SPN-CON-0005 (stemfie.org).stl

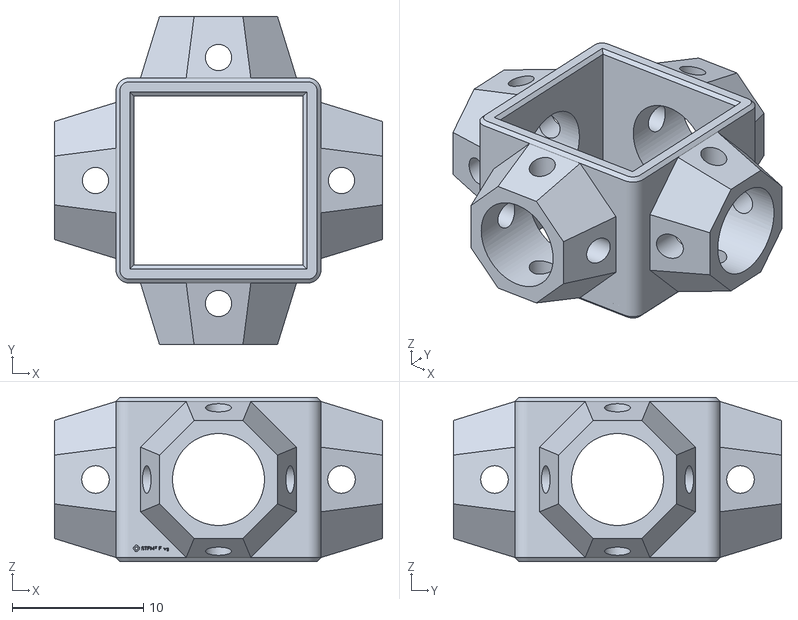
[picture p82: CAD file, 2021-05-27]
Connectors/Beam Through-Hole/Connector BEM THR-H SFT 4W BU01x01x01x00.50 - SPN-CON-0005 (stemfie.org).stl
25.0 x 25.0 x 12.5
