Stemfie3D/STEMFIE-file-repository/Miscellaneous/Ornaments/Ornament Star - Five-Pointed (threaded) BU01x02x02 - SPN-ORN-0001 (stemfie.org) [without 3D-printing supports].stl

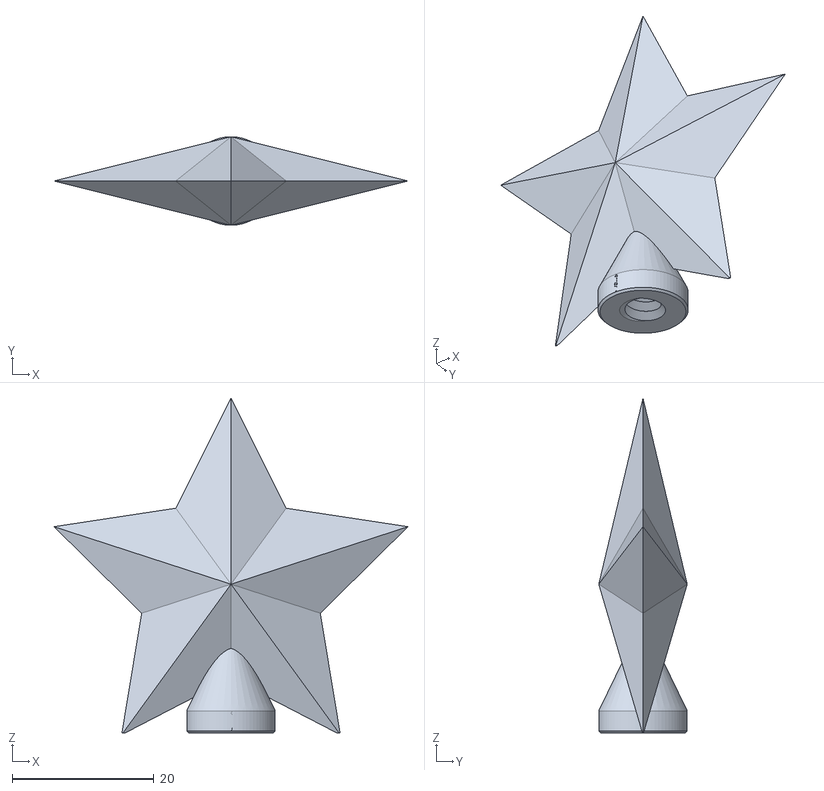
[picture p83: CAD file, 2021-05-27]
Miscellaneous/Ornaments/Ornament Star - Five-Pointed (threaded) BU01x02x02 - SPN-ORN-0001 (stemfie.org) [without 3D-printing supports].stl
50.0 x 12.5 x 47.3
