Stemfie3D/STEMFIE-file-repository/Miscellaneous/Signs/Beams/Sign URL BEM STR ESS BU10x01x01 - SPN-SGN-0016 (stemfie.org).stl

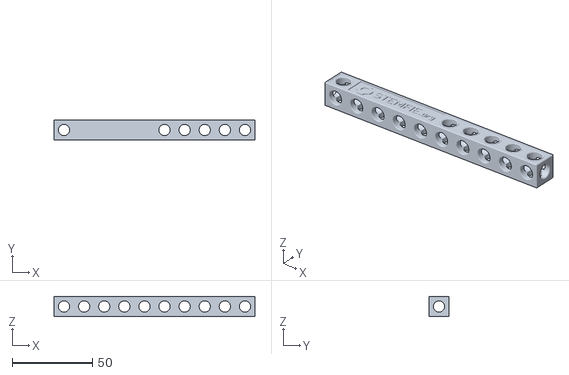
[picture p84: CAD file, 2022-04-05]
Miscellaneous/Signs/Beams/Sign URL BEM STR ESS BU10x01x01 - SPN-SGN-0016 (stemfie.org).stl
125.0 x 12.5 x 12.5
