Stemfie3D/STEMFIE-file-repository/Miscellaneous/Signs/Build Plates/Sign URL BEM BU04x02x00.25 - SPN-SGN-0006 (stemfie.org) 10x 3D-printing build plate.3mf

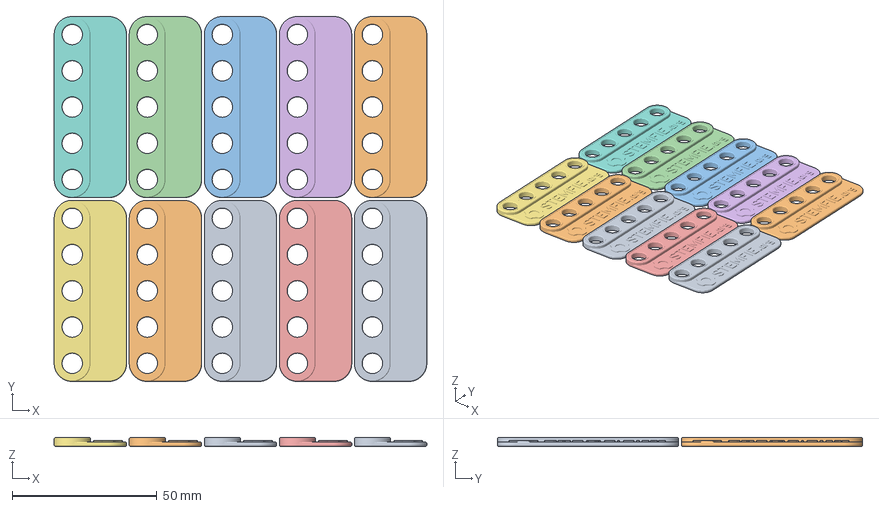
[picture p85: CAD file, 2021-05-27]
Miscellaneous/Signs/Build Plates/Sign URL BEM BU04x02x00.25 - SPN-SGN-0006 (stemfie.org) 10x 3D-printing build plate.3mf
128.5 x 125.9 x 3.12 mm
