Stemfie3D/STEMFIE-file-repository/Miscellaneous/Signs/Sign URL SLTD LAY BU04x02x01 - SPN-SGN-0012 (stemfie.org).stl

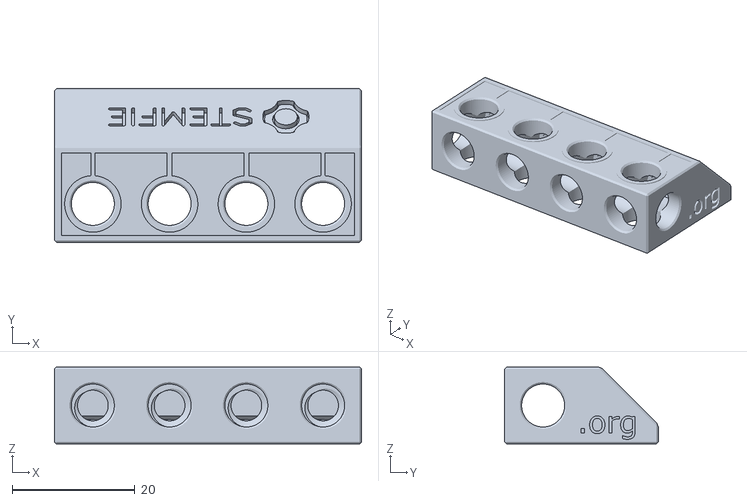
[picture p86: CAD file, 2022-06-21]
Miscellaneous/Signs/Sign URL SLTD LAY BU04x02x01 - SPN-SGN-0012 (stemfie.org).stl
50.0 x 25.0 x 12.5
