Stemfie3D/STEMFIE-file-repository/Plates/3 - Triangular/Plate TRI BU05x00.25 - SPN-PLT-0016 (stemfie.org).stl

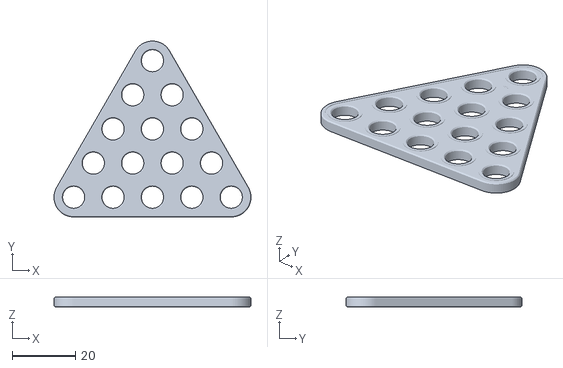
[picture p87: CAD file, 2023-01-02]
Plates/3 - Triangular/Plate TRI BU05x00.25 - SPN-PLT-0016 (stemfie.org).stl
62.5 x 55.8 x 3.13
