Stemfie3D/STEMFIE-file-repository/Plates/4 - Square/Plate SQR BU08x00.25 - SPN-PLT-0043 (stemfie.org).stl

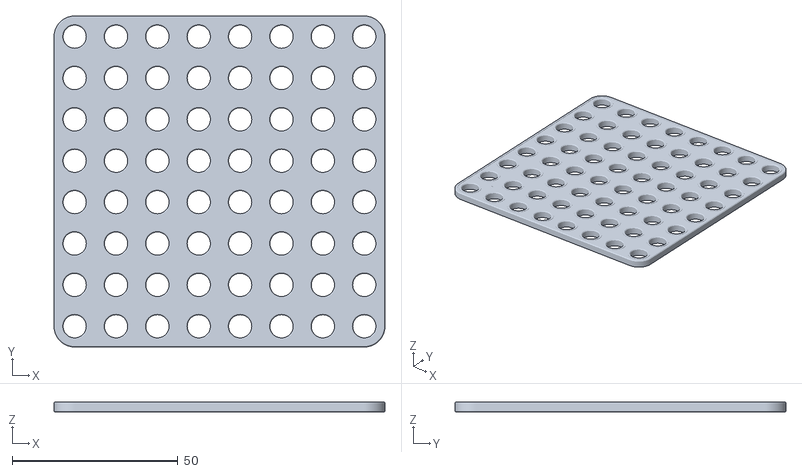
[picture p88: CAD file, 2023-01-02]
Plates/4 - Square/Plate SQR BU08x00.25 - SPN-PLT-0043 (stemfie.org).stl
100.0 x 100.0 x 3.13
