Stemfie3D/STEMFIE-file-repository/Plates/6 - Hexagonal/Plate HEX BU07x00.25 - SPN-PLT-0003 (stemfie.org).stl

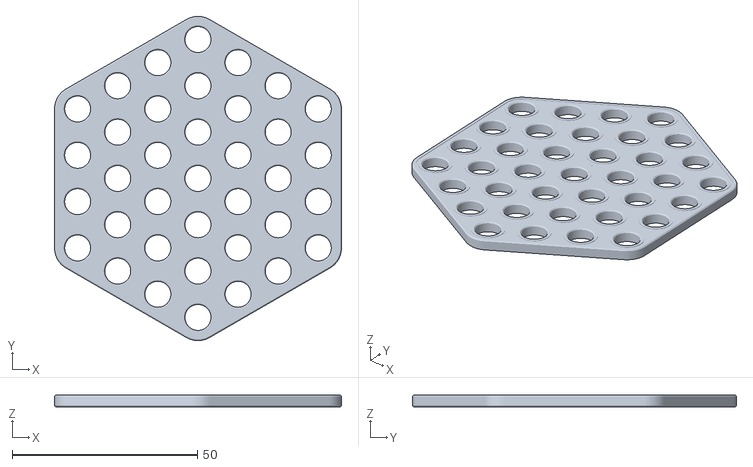
[picture p89: CAD file, 2023-01-02]
Plates/6 - Hexagonal/Plate HEX BU07x00.25 - SPN-PLT-0003 (stemfie.org).stl
77.5 x 87.5 x 3.13
