Stemfie3D/STEMFIE-file-repository/Projects/SPS-000002 - Desktop Christmas Tree/Build Plates/SPS-000002 - Desktop Christmas Tree - Foot - Gray (stemfie.org).3mf

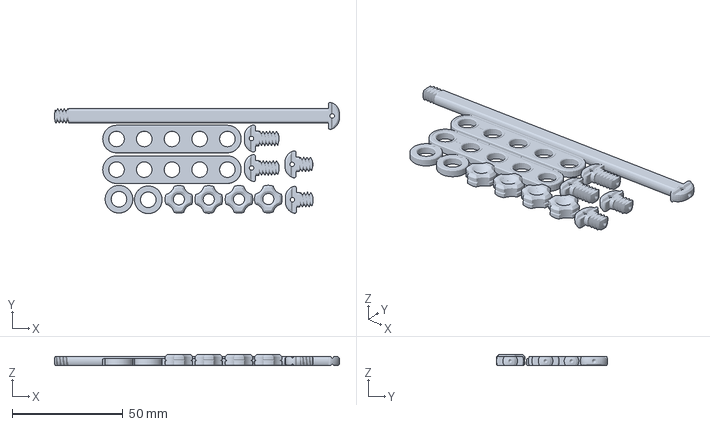
[picture p90: CAD file, 2022-02-20]
Projects/SPS-000002 - Desktop Christmas Tree/Build Plates/SPS-000002 - Desktop Christmas Tree - Foot - Gray (stemfie.org).3mf
128.6 x 50.2 x 5.00 mm
