Stemfie3D/STEMFIE-file-repository/Shafts/Plain/Shaft PLN BU23.00 - SPN-SFT-0092 (stemfie.org).stl

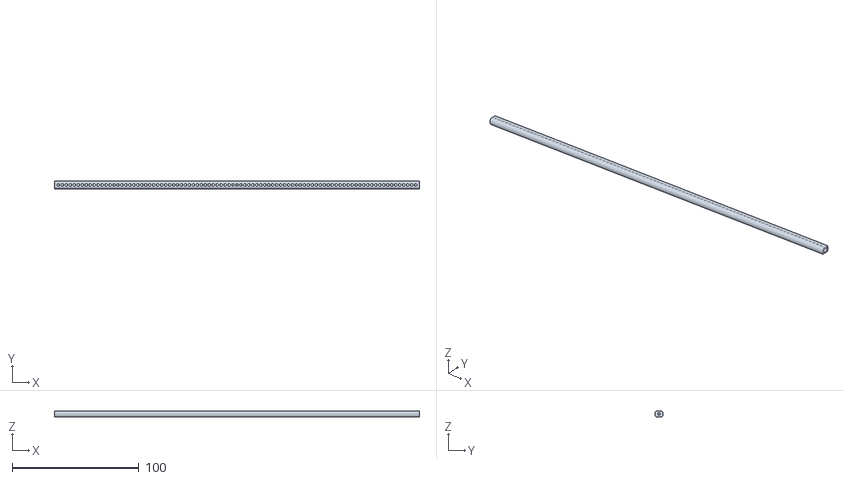
[picture p91: CAD file, 2023-08-03]
Shafts/Plain/Shaft PLN BU23.00 - SPN-SFT-0092 (stemfie.org).stl
287.5 x 6.60 x 5.00
