Stemfie3D/STEMFIE-file-repository/Tools/Storage/Parts Drawer/Parts Storage Drawer Section Divider TRV BU04.00x03.75 - SPN-TOL-0050 (stemfie.org).stl

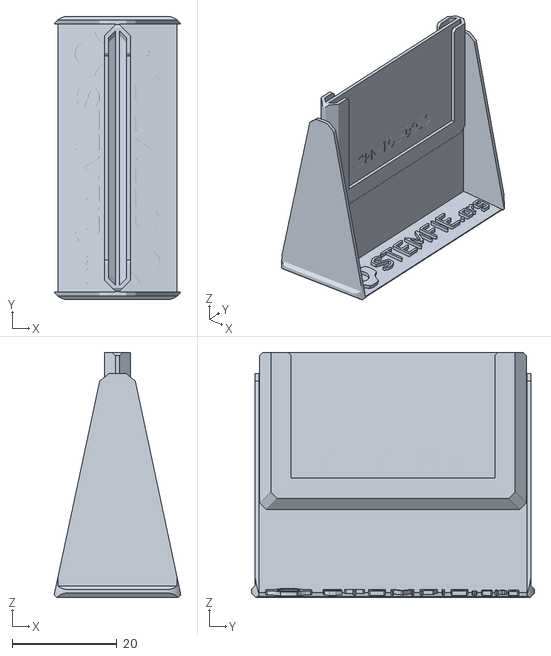
[picture p92: CAD file, 2023-03-22]
Tools/Storage/Parts Drawer/Parts Storage Drawer Section Divider TRV BU04.00x03.75 - SPN-TOL-0050 (stemfie.org).stl
24.2 x 54.1 x 46.8
