Stemfie3D/STEMFIE-file-repository/Beams/Angled/T-shaped Symmetric/Beam AGD TSH SYM ESS BU17x13x01 - SPN-BEM-1144 (stemfie.org).stl

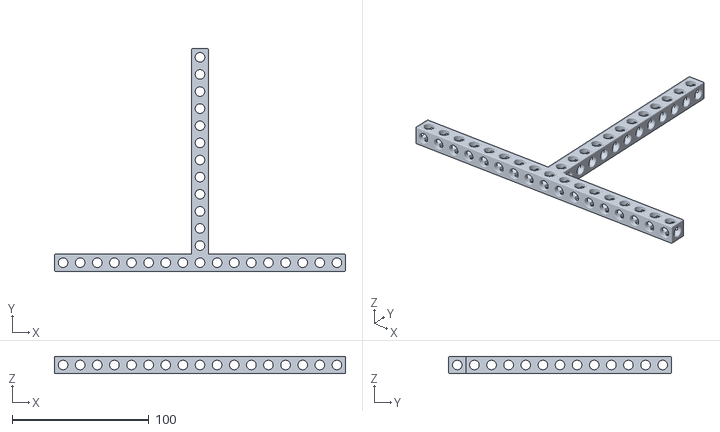
[picture p93: CAD file, 2022-01-30]
Beams/Angled/T-shaped Symmetric/Beam AGD TSH SYM ESS BU17x13x01 - SPN-BEM-1144 (stemfie.org).stl
212.5 x 162.5 x 12.5
