Stemfie3D/STEMFIE-file-repository/Beams/Angled/T-shaped Symmetric/Build Plates/Beam AGD TSH SYM ESS BU03x20x01 - SPN-BEM-1018 (stemfie.org) 12x 3D-printing build plate.3mf

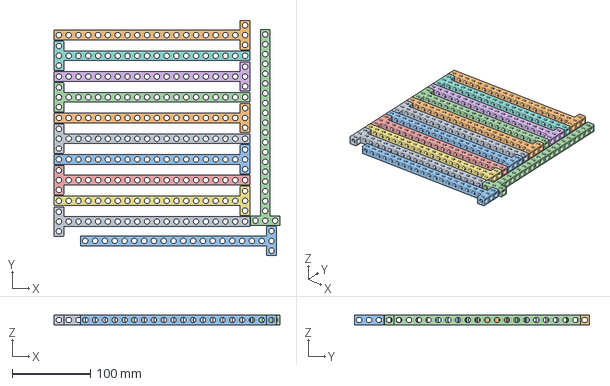
[picture p94: CAD file, 2022-04-08]
Beams/Angled/T-shaped Symmetric/Build Plates/Beam AGD TSH SYM ESS BU03x20x01 - SPN-BEM-1018 (stemfie.org) 12x 3D-printing build plate.3mf
288.3 x 300.0 x 12.5 mm
