Stemfie3D/STEMFIE-file-repository/Beams/Angled/U-shaped Symmetric/Beam AGD USH SYM ESS BU09x05x01 - SPN-BEM-0426 (stemfie.org).stl

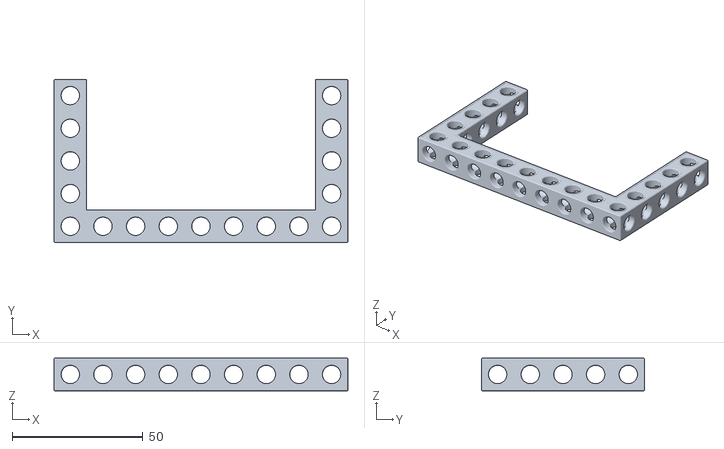
[picture p95: CAD file, 2022-04-05]
Beams/Angled/U-shaped Symmetric/Beam AGD USH SYM ESS BU09x05x01 - SPN-BEM-0426 (stemfie.org).stl
112.5 x 62.5 x 12.5
