Stemfie3D/STEMFIE-file-repository/Beams/Angled/U-shaped Symmetric/Build Plates/Beam AGD USH SYM ESS BU04x11x01 - SPN-BEM-0329 (stemfie.org) 6x 3D Printing Build Plate.3mf

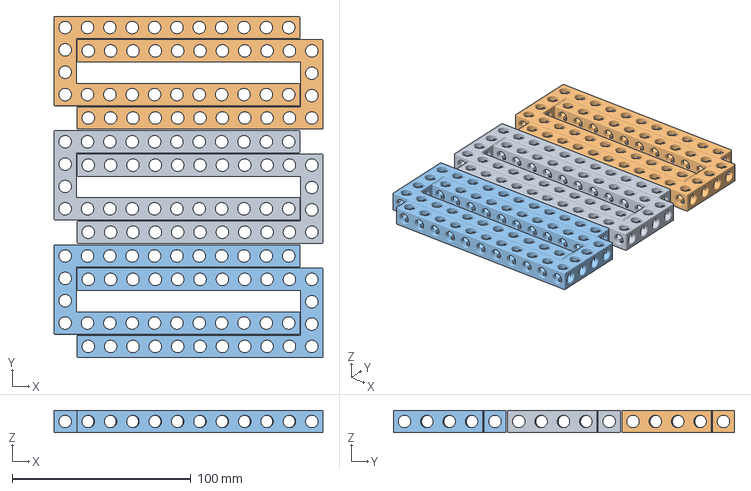
[picture p96: CAD file, 2023-02-07]
Beams/Angled/U-shaped Symmetric/Build Plates/Beam AGD USH SYM ESS BU04x11x01 - SPN-BEM-0329 (stemfie.org) 6x 3D Printing Build Plate.3mf
150.4 x 190.8 x 12.5 mm
