Stemfie3D/STEMFIE-file-repository/Beams/Straight/Box-section/Beam STR BXS ESS BU05.75x01.00x01.00x00.25x00.125 - SPN-BEM-0020 (stemfie.org).stl

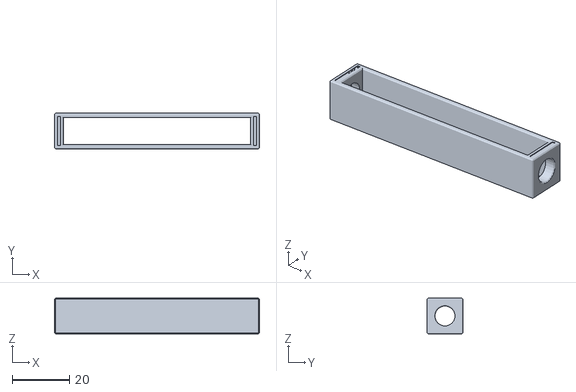
[picture p97: CAD file, 2021-05-27]
Beams/Straight/Box-section/Beam STR BXS ESS BU05.75x01.00x01.00x00.25x00.125 - SPN-BEM-0020 (stemfie.org).stl
71.9 x 12.5 x 12.5
