Stemfie3D/STEMFIE-file-repository/Beams/Straight/Box-section/Build Plates/Beam STR BXS ESS BU03.75x01.00x01.00x00.25x00.125 - SPN-BEM-0012 (stemfie.org) 26x 3D-printing build plate.3mf

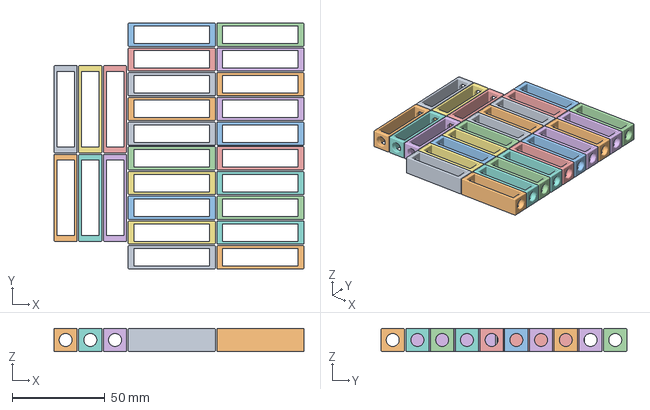
[picture p98: CAD file, 2022-04-08]
Beams/Straight/Box-section/Build Plates/Beam STR BXS ESS BU03.75x01.00x01.00x00.25x00.125 - SPN-BEM-0012 (stemfie.org) 26x 3D-printing build plate.3mf
134.4 x 132.2 x 12.5 mm
