Stemfie3D/STEMFIE-file-repository/Beams/Straight/Square Ends/Build Plates/Beam STR ESS BU25x01x01 - SPN-BEM-0062 (stemfie.org) 36x 3D-printing build plate.3mf

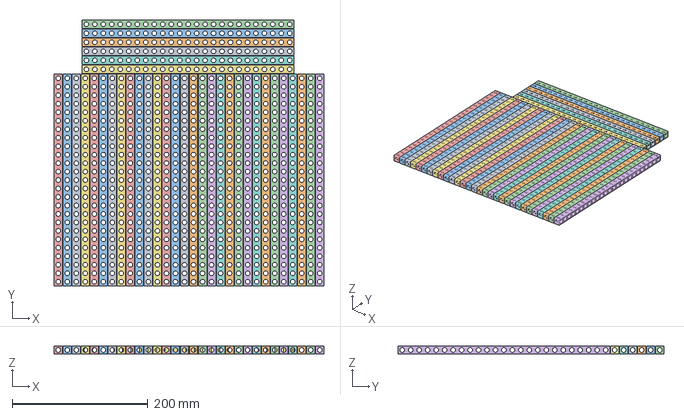
[picture p99: CAD file, 2022-04-08]
Beams/Straight/Square Ends/Build Plates/Beam STR ESS BU25x01x01 - SPN-BEM-0062 (stemfie.org) 36x 3D-printing build plate.3mf
398.2 x 392.3 x 12.5 mm
