Stemfie3D/STEMFIE-file-repository/Beams/Straight/Threaded Ends/Beam STR ERHRH DE ESS BU02x01x01 - SPN-BEM-0801 (stemfie.org).stl

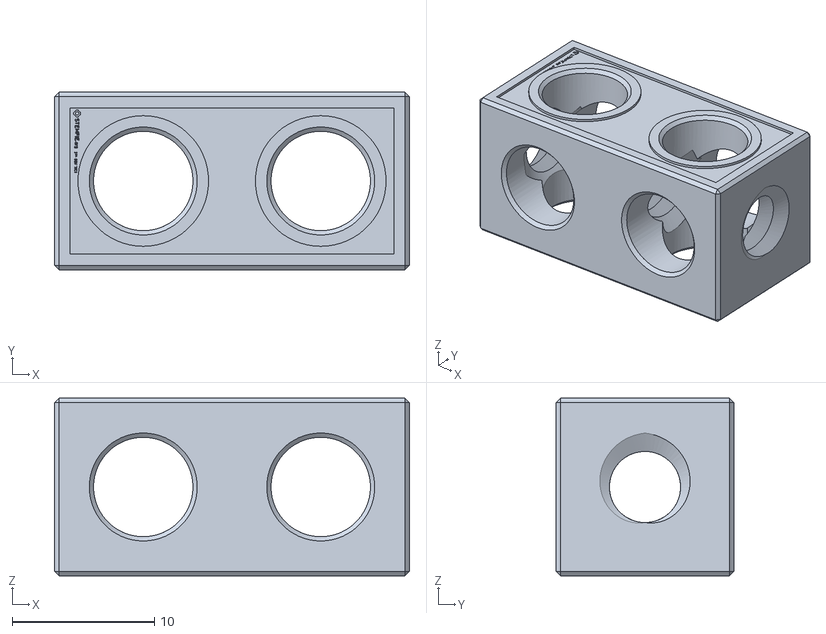
[picture p100: CAD file, 2021-07-01]
Beams/Straight/Threaded Ends/Beam STR ERHRH DE ESS BU02x01x01 - SPN-BEM-0801 (stemfie.org).stl
25.0 x 12.5 x 12.5
