Stemfie3D/STEMFIE-file-repository/Beams/Straight/Threaded Ends/Build Plates/Beam STR ERHRH DE ESS BU05x01x01 - SPN-BEM-0804 (stemfie.org) 22x 3D-printing build plate.3mf

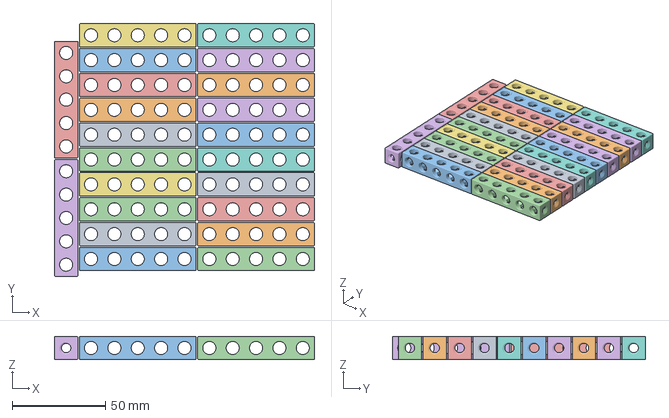
[picture p101: CAD file, 2022-04-08]
Beams/Straight/Threaded Ends/Build Plates/Beam STR ERHRH DE ESS BU05x01x01 - SPN-BEM-0804 (stemfie.org) 22x 3D-printing build plate.3mf
139.1 x 135.3 x 12.5 mm
