Stemfie3D/STEMFIE-file-repository/Braces/Angled/90 Degrees Asymmetric/Brace AGD 90 ASYM ERR BU15x16x01x00.25 - SPN-BRC-1156 (stemfie.org).stl

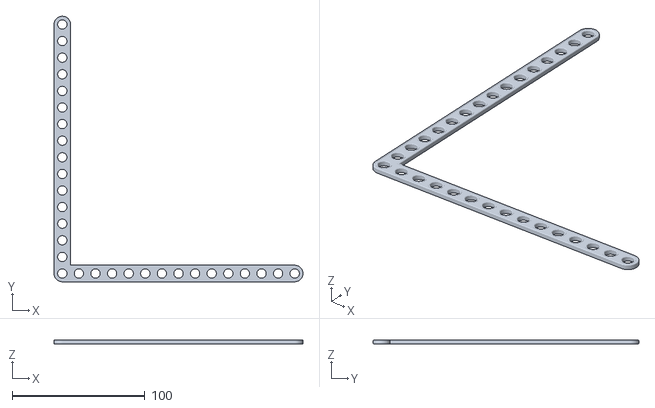
[picture p102: CAD file, 2022-02-10]
Braces/Angled/90 Degrees Asymmetric/Brace AGD 90 ASYM ERR BU15x16x01x00.25 - SPN-BRC-1156 (stemfie.org).stl
187.5 x 200.0 x 3.13
