Stemfie3D/STEMFIE-file-repository/Braces/Straight/Slotted Both Ends/Brace STR SLT BE SYM ERR BU16x01x00.25x03 - SPN-BRC-0336 (stemfie.org).stl

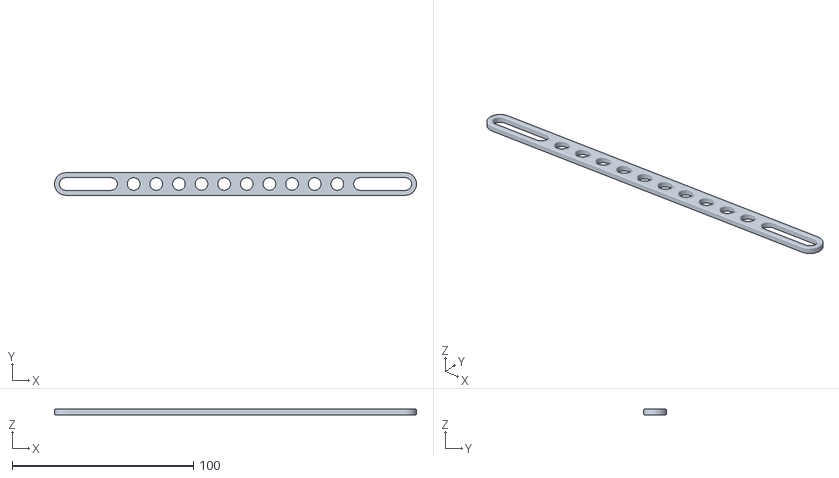
[picture p103: CAD file, 2021-05-27]
Braces/Straight/Slotted Both Ends/Brace STR SLT BE SYM ERR BU16x01x00.25x03 - SPN-BRC-0336 (stemfie.org).stl
199.9 x 12.5 x 3.12
