Stemfie3D/STEMFIE-file-repository/Braces/Straight/Slotted Centered/Brace STR SLT CNT ERR BU20x01x00.25x14 - SPN-BRC-0416 (stemfie.org).stl

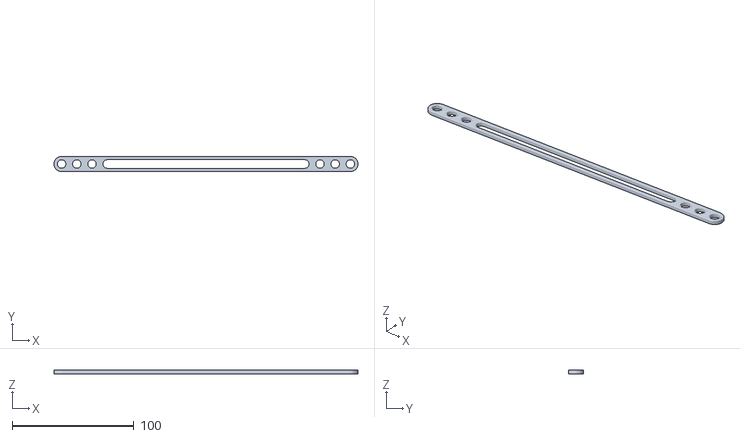
[picture p104: CAD file, 2021-05-27]
Braces/Straight/Slotted Centered/Brace STR SLT CNT ERR BU20x01x00.25x14 - SPN-BRC-0416 (stemfie.org).stl
250.0 x 12.5 x 3.13
