Stemfie3D/STEMFIE-file-repository/Braces/Straight/Slotted Full Length/Brace STR SLT FL ERR BU11x01x00.25 - SPN-BRC-0112 (stemfie.org).stl

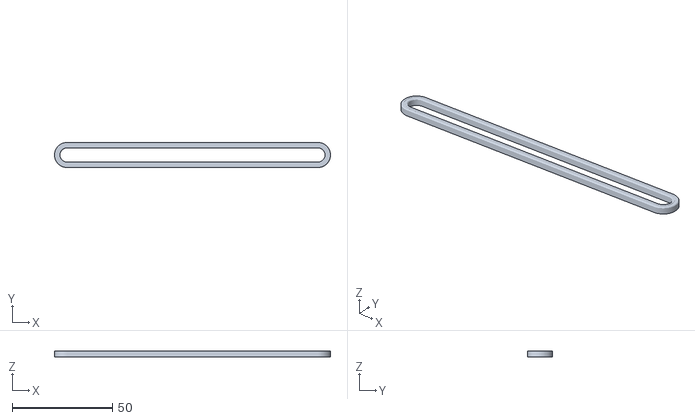
[picture p105: CAD file, 2021-05-27]
Braces/Straight/Slotted Full Length/Brace STR SLT FL ERR BU11x01x00.25 - SPN-BRC-0112 (stemfie.org).stl
137.5 x 12.5 x 3.13
