Stemfie3D/STEMFIE-file-repository/Braces/Straight/Slotted Single End/Brace STR SLT SE ERR BU13x01x00.25x05 - SPN-BRC-0180 (stemfie.org).stl

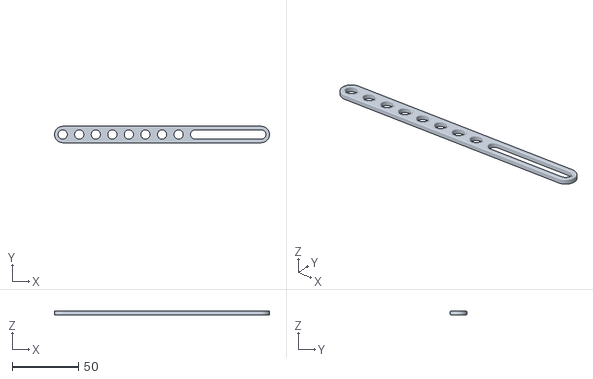
[picture p106: CAD file, 2021-05-27]
Braces/Straight/Slotted Single End/Brace STR SLT SE ERR BU13x01x00.25x05 - SPN-BRC-0180 (stemfie.org).stl
162.4 x 12.5 x 3.12
