Stemfie3D/STEMFIE-file-repository/Braces/Straight/Standard/Brace STR STD ERR BU32x01x00.25 - SPN-BRC-0031 (stemfie.org).stl

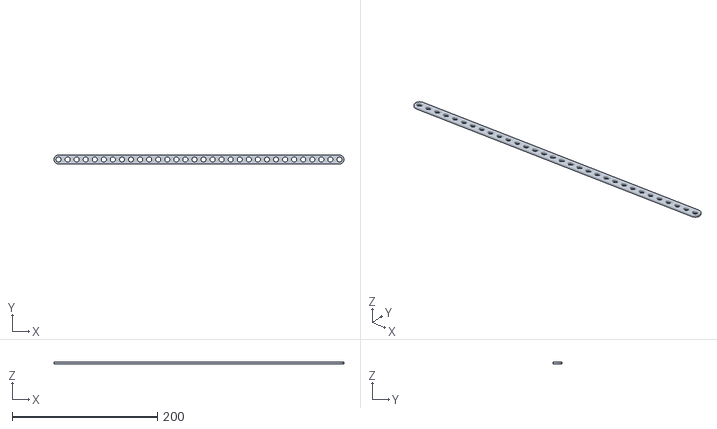
[picture p107: CAD file, 2021-05-27]
Braces/Straight/Standard/Brace STR STD ERR BU32x01x00.25 - SPN-BRC-0031 (stemfie.org).stl
400.0 x 12.5 x 3.12
