Stemfie3D/STEMFIE-file-repository/Braces/Straight/Standard/Build Plates/Brace STR ERR BU10x01x00.25 - SPN-BRC-0009 (stemfie.org) 11x 3D-printing build plate.3mf

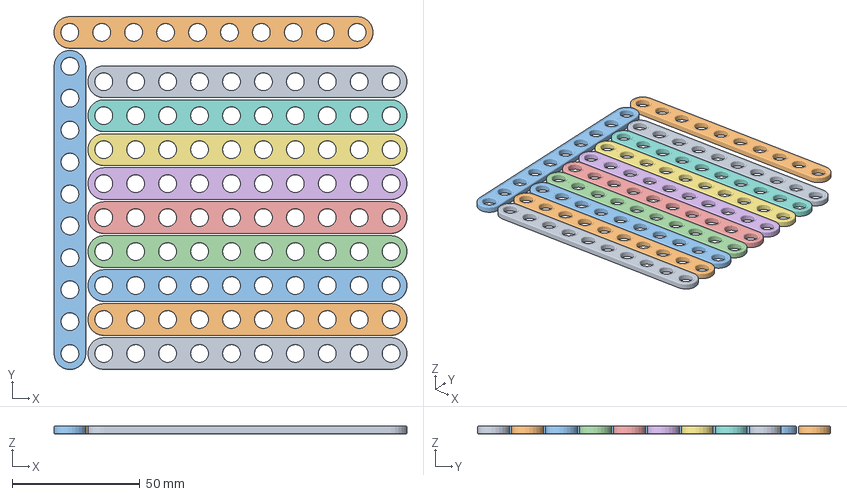
[picture p108: CAD file, 2021-05-27]
Braces/Straight/Standard/Build Plates/Brace STR ERR BU10x01x00.25 - SPN-BRC-0009 (stemfie.org) 11x 3D-printing build plate.3mf
138.2 x 138.2 x 3.12 mm
