Stemfie3D/STEMFIE-file-repository/Connectors/Beam Through-Hole/Connector BEM THR-H SFT 1W BU01x01x01x00.50 - SPN-CON-0001 (stemfie.org).stl

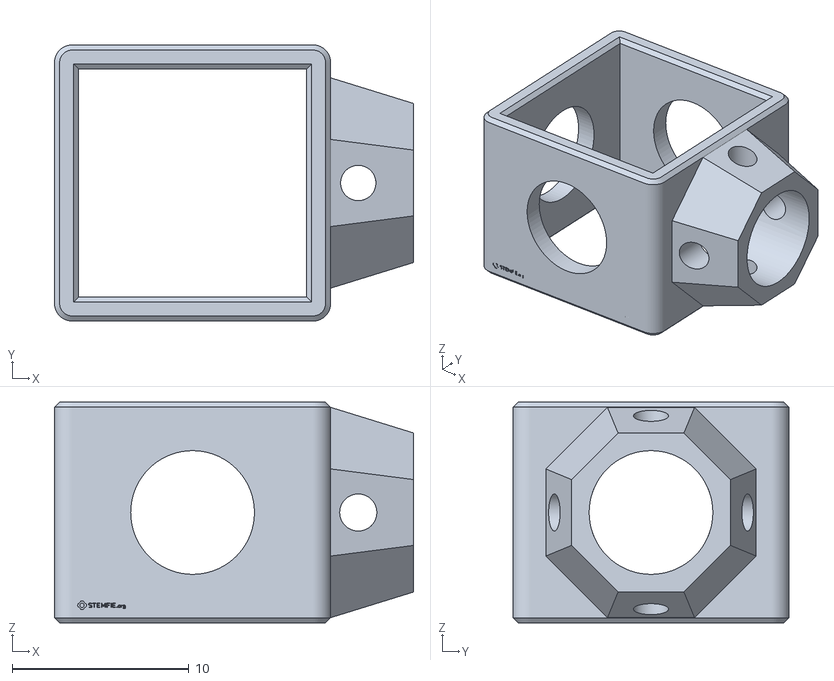
[picture p109: CAD file, 2021-05-27]
Connectors/Beam Through-Hole/Connector BEM THR-H SFT 1W BU01x01x01x00.50 - SPN-CON-0001 (stemfie.org).stl
20.3 x 15.6 x 12.5
