Stemfie3D/STEMFIE-file-repository/Miscellaneous/Signs/Beams/Sign URL BEM STR ESS BU20x01x01 - SPN-SGN-0026 (stemfie.org).stl

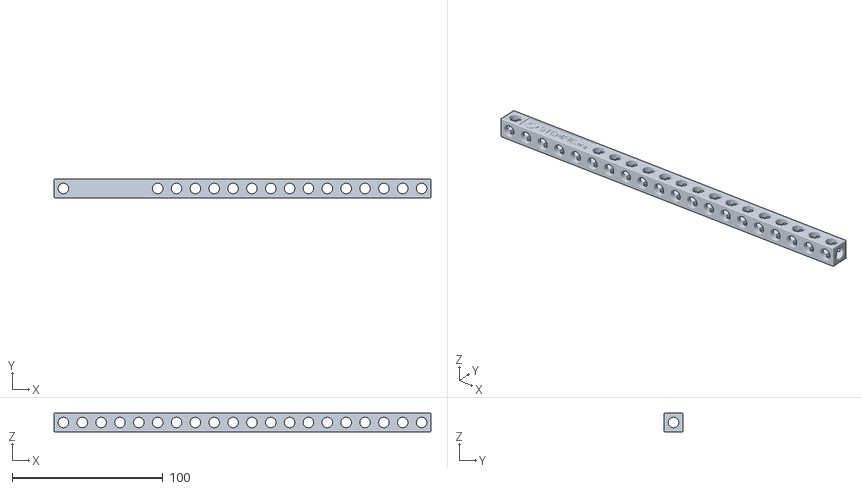
[picture p110: CAD file, 2022-04-05]
Miscellaneous/Signs/Beams/Sign URL BEM STR ESS BU20x01x01 - SPN-SGN-0026 (stemfie.org).stl
250.0 x 12.5 x 12.5
