Stemfie3D/STEMFIE-file-repository/Miscellaneous/Signs/Sign URL SLTD STA BU03x02x01 - SPN-SGN-0003 (stemfie.org).stl

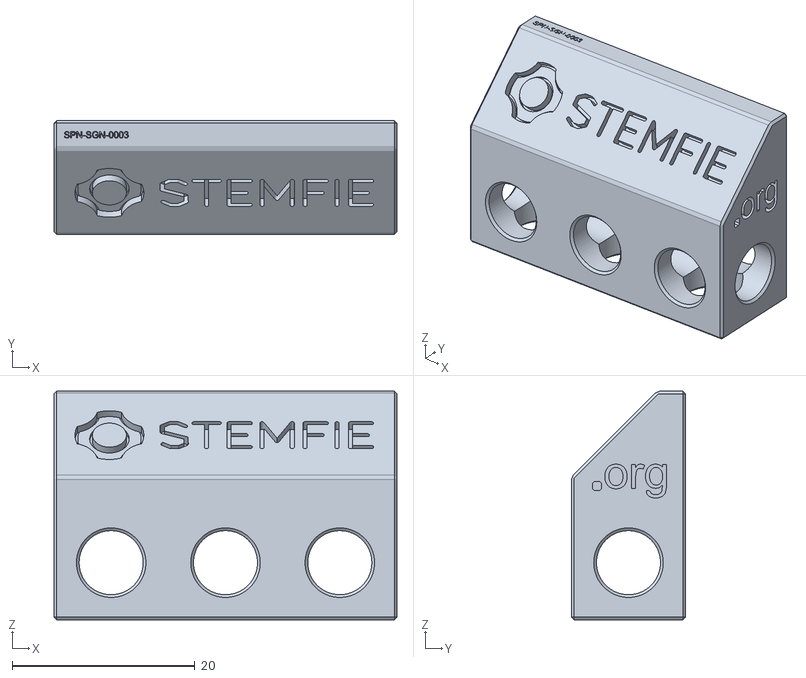
[picture p111: CAD file, 2021-08-24]
Miscellaneous/Signs/Sign URL SLTD STA BU03x02x01 - SPN-SGN-0003 (stemfie.org).stl
37.5 x 12.5 x 25.0
