Stemfie3D/STEMFIE-file-repository/Plates/3 - Triangular/Plate TRI BU12x00.25 - SPN-PLT-0023 (stemfie.org).stl

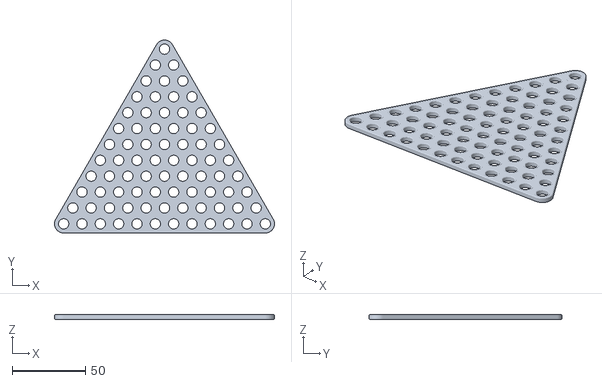
[picture p112: CAD file, 2023-01-02]
Plates/3 - Triangular/Plate TRI BU12x00.25 - SPN-PLT-0023 (stemfie.org).stl
150.0 x 131.6 x 3.13
