Stemfie3D/STEMFIE-file-repository/Plates/4 - Square/Plate SQR BU10x00.25 - SPN-PLT-0045 (stemfie.org).stl

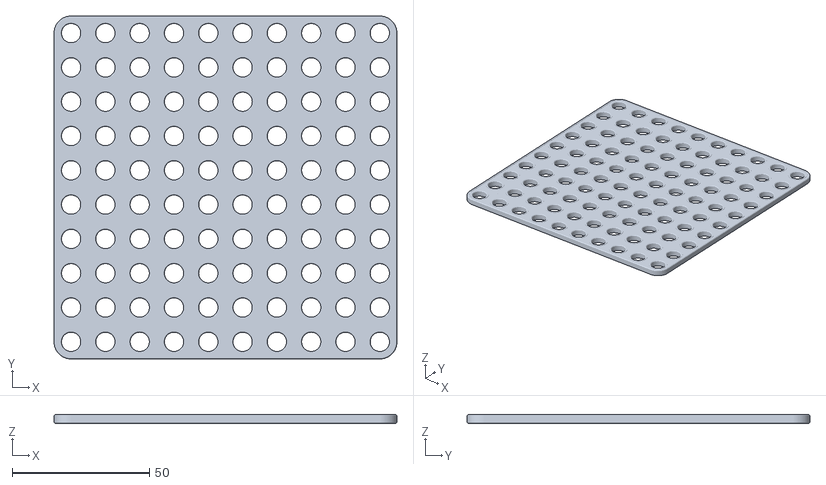
[picture p113: CAD file, 2023-01-02]
Plates/4 - Square/Plate SQR BU10x00.25 - SPN-PLT-0045 (stemfie.org).stl
125.0 x 125.0 x 3.13
