Stemfie3D/STEMFIE-file-repository/Plates/6 - Hexagonal/Plate HEX BU09x00.25 - SPN-PLT-0004 (stemfie.org).stl

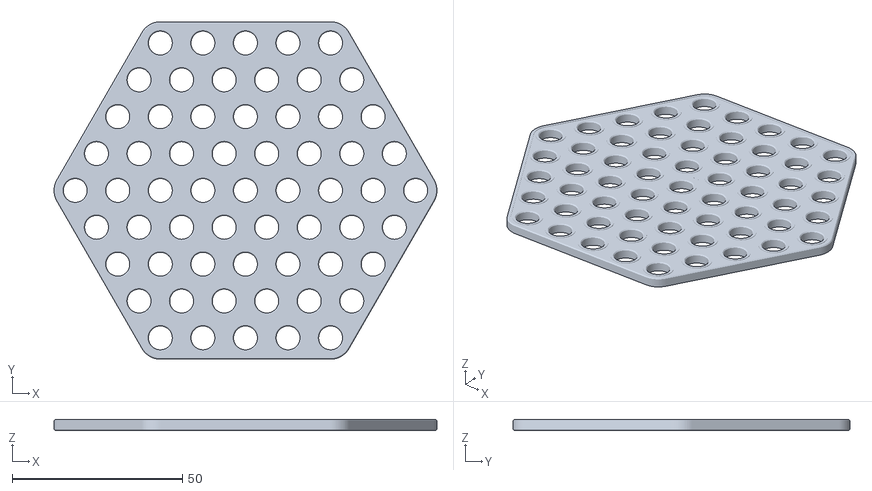
[picture p114: CAD file, 2023-01-02]
Plates/6 - Hexagonal/Plate HEX BU09x00.25 - SPN-PLT-0004 (stemfie.org).stl
112.5 x 99.1 x 3.13
