Stemfie3D/STEMFIE-file-repository/Projects/SPS-000001 - Rubber-band-driven car/Build plates/SPS-000001 - Rubber-band-driven car - Beams Braces (stemfie.org).3mf

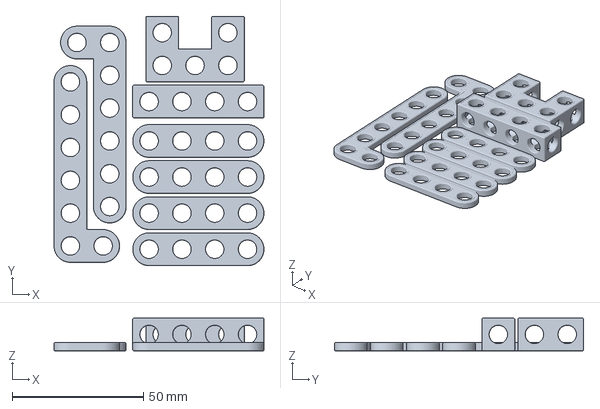
[picture p115: CAD file, 2022-02-20]
Projects/SPS-000001 - Rubber-band-driven car/Build plates/SPS-000001 - Rubber-band-driven car - Beams Braces (stemfie.org).3mf
80.0 x 95.0 x 12.5 mm
