Stemfie3D/STEMFIE-file-repository/Projects/SPS-000002 - Desktop Christmas Tree/Build Plates/SPS-000002 - Desktop Christmas Tree - Star - Yellow - Instructions (stemfie.org).3mf

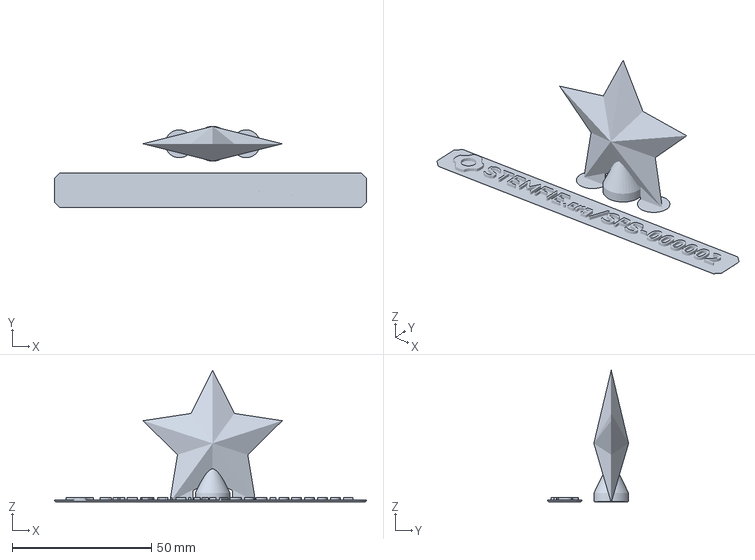
[picture p116: CAD file, 2022-02-20]
Projects/SPS-000002 - Desktop Christmas Tree/Build Plates/SPS-000002 - Desktop Christmas Tree - Star - Yellow - Instructions (stemfie.org).3mf
112.0 x 29.2 x 47.3 mm
