Stemfie3D/STEMFIE-file-repository/Shafts/Plain/Shaft PLN BU16.00 - SPN-SFT-0064 (stemfie.org).stl

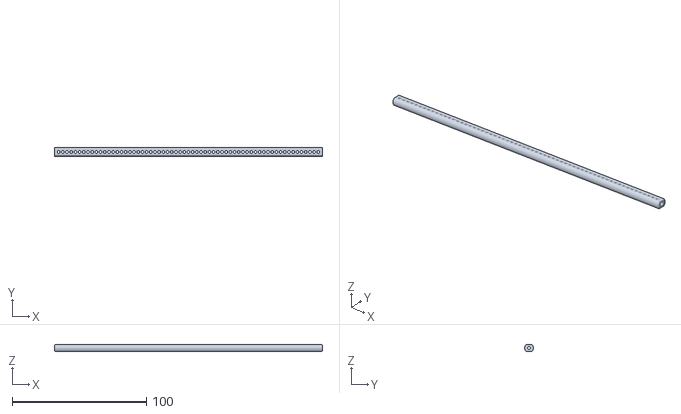
[picture p117: CAD file, 2023-08-03]
Shafts/Plain/Shaft PLN BU16.00 - SPN-SFT-0064 (stemfie.org).stl
200.0 x 6.59 x 5.00
