Stemfie3D/STEMFIE-file-repository/Tools/Storage/Parts Drawer/Parts Storage Drawer BU09.00x10.00x03.75 - SPN-TOL-0047 (stemfie.org).stl

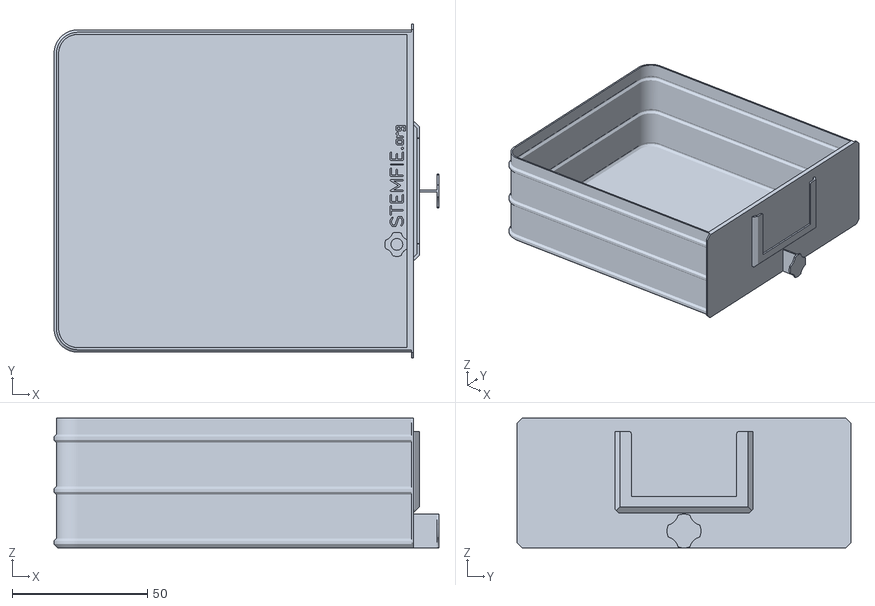
[picture p118: CAD file, 2023-03-22]
Tools/Storage/Parts Drawer/Parts Storage Drawer BU09.00x10.00x03.75 - SPN-TOL-0047 (stemfie.org).stl
142.3 x 123.5 x 48.0
