Stemfie3D/STEMFIE-file-repository/Beams/Angled/T-shaped Symmetric/Beam AGD TSH SYM ESS BU07x19x01 - SPN-BEM-1055 (stemfie.org).stl

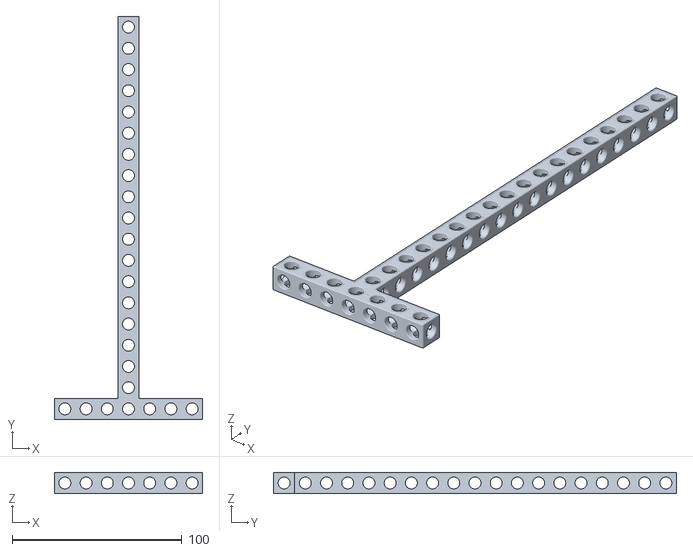
[picture p119: CAD file, 2022-01-30]
Beams/Angled/T-shaped Symmetric/Beam AGD TSH SYM ESS BU07x19x01 - SPN-BEM-1055 (stemfie.org).stl
87.5 x 237.5 x 12.5
