Stemfie3D/STEMFIE-file-repository/Beams/Angled/T-shaped Symmetric/Build Plates/Beam AGD TSH SYM ESS BU03x10x01 - SPN-BEM-1008 (stemfie.org) 4x 3D-printing build plate.3mf

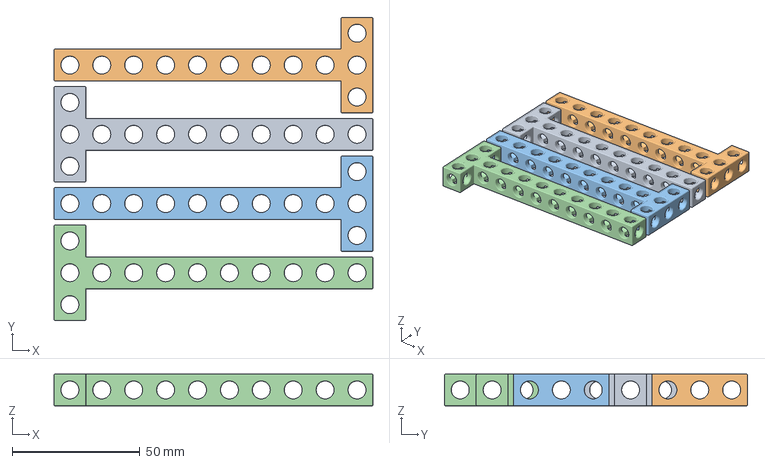
[picture p120: CAD file, 2022-04-08]
Beams/Angled/T-shaped Symmetric/Build Plates/Beam AGD TSH SYM ESS BU03x10x01 - SPN-BEM-1008 (stemfie.org) 4x 3D-printing build plate.3mf
125.0 x 118.9 x 12.5 mm
