Stemfie3D/STEMFIE-file-repository/Beams/Angled/U-shaped Symmetric/Beam AGD USH SYM ESS BU05x13x01 - SPN-BEM-0350 (stemfie.org).stl

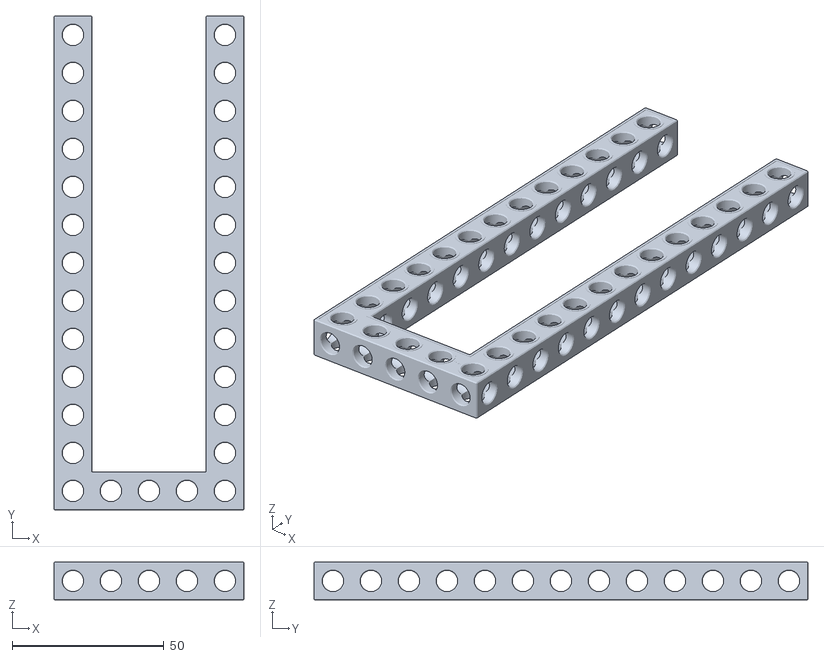
[picture p121: CAD file, 2022-04-05]
Beams/Angled/U-shaped Symmetric/Beam AGD USH SYM ESS BU05x13x01 - SPN-BEM-0350 (stemfie.org).stl
62.5 x 162.5 x 12.5
