Stemfie3D/STEMFIE-file-repository/Beams/Angled/U-shaped Symmetric/Build Plates/Beam AGD USH SYM ESS BU04x18x01 - SPN-BEM-0336 (stemfie.org) 8x 3D Printing Build Plate.3mf

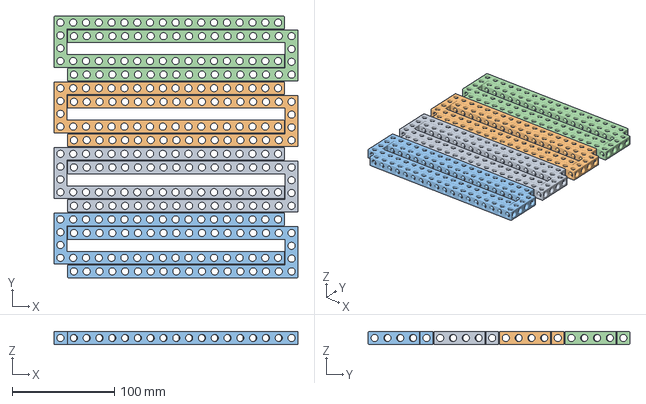
[picture p122: CAD file, 2023-02-07]
Beams/Angled/U-shaped Symmetric/Build Plates/Beam AGD USH SYM ESS BU04x18x01 - SPN-BEM-0336 (stemfie.org) 8x 3D Printing Build Plate.3mf
238.2 x 255.4 x 12.5 mm
