Stemfie3D/STEMFIE-file-repository/Beams/Straight/Box-section/Beam STR BXS ESS BU02.50x01.00x01.00x00.25x00.125 - SPN-BEM-0007 (stemfie.org).stl

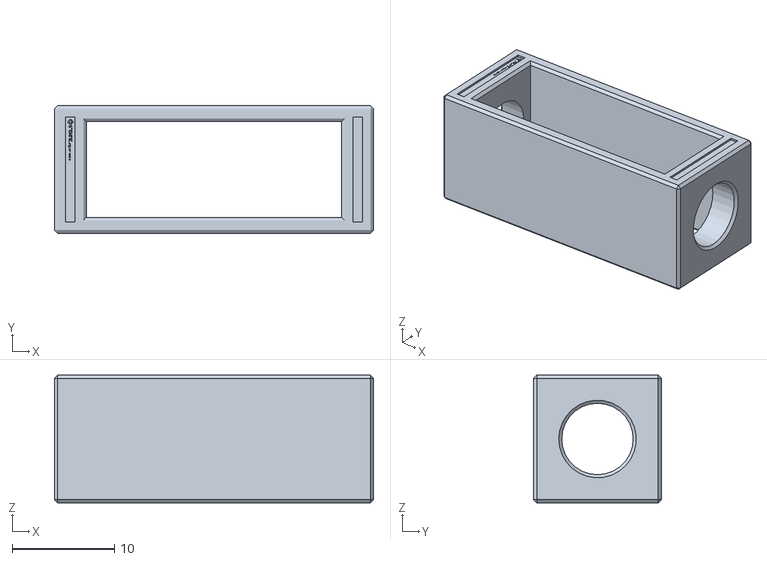
[picture p123: CAD file, 2021-05-27]
Beams/Straight/Box-section/Beam STR BXS ESS BU02.50x01.00x01.00x00.25x00.125 - SPN-BEM-0007 (stemfie.org).stl
31.2 x 12.5 x 12.5
