Stemfie3D/STEMFIE-file-repository/Beams/Straight/Box-section/Build Plates/Beam STR BXS ESS BU09.50x01.00x01.00x00.25x00.125 - SPN-BEM-0035 (stemfie.org) 11x 3D-printing build plate.3mf

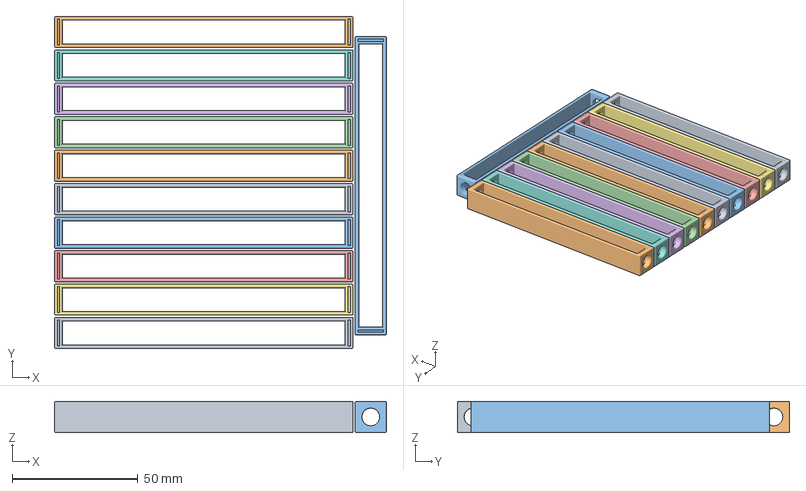
[picture p124: CAD file, 2022-04-08]
Beams/Straight/Box-section/Build Plates/Beam STR BXS ESS BU09.50x01.00x01.00x00.25x00.125 - SPN-BEM-0035 (stemfie.org) 11x 3D-printing build plate.3mf
132.1 x 132.2 x 12.5 mm
