Stemfie3D/STEMFIE-file-repository/Beams/Straight/Square Ends/Beam STR ESS BU34x01x01 - SPN-BEM-0071 (stemfie.org).stl

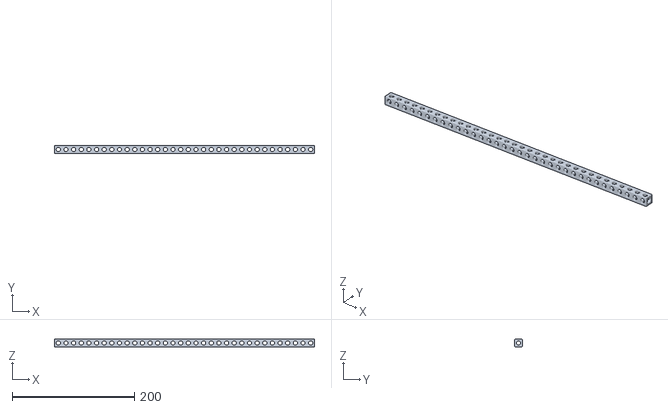
[picture p125: CAD file, 2021-05-30]
Beams/Straight/Square Ends/Beam STR ESS BU34x01x01 - SPN-BEM-0071 (stemfie.org).stl
425.0 x 12.5 x 12.5
