Stemfie3D/STEMFIE-file-repository/Beams/Straight/Square Ends/Build Plates/Beam STR ESS BU17x01x01 - SPN-BEM-0054 (stemfie.org) 28x 3D-printing build plate.3mf

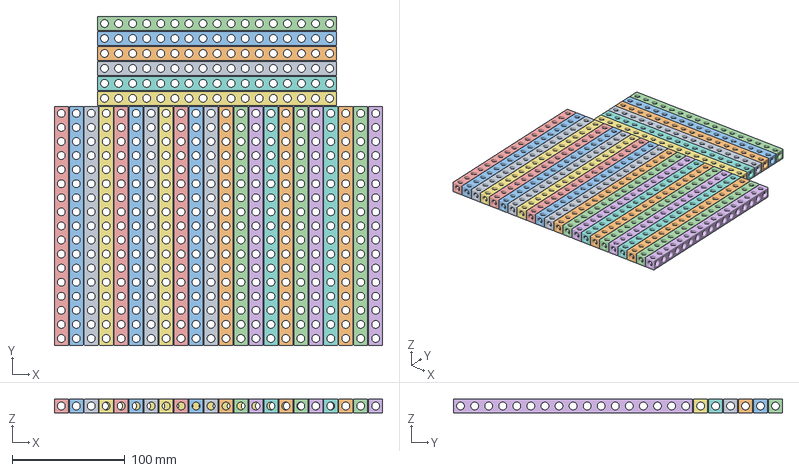
[picture p126: CAD file, 2022-04-08]
Beams/Straight/Square Ends/Build Plates/Beam STR ESS BU17x01x01 - SPN-BEM-0054 (stemfie.org) 28x 3D-printing build plate.3mf
291.8 x 292.3 x 12.5 mm
