Stemfie3D/STEMFIE-file-repository/3D-printing/Build Plates/STEMFIE Essentials/STEMFIE Essentials (thumbnail).png

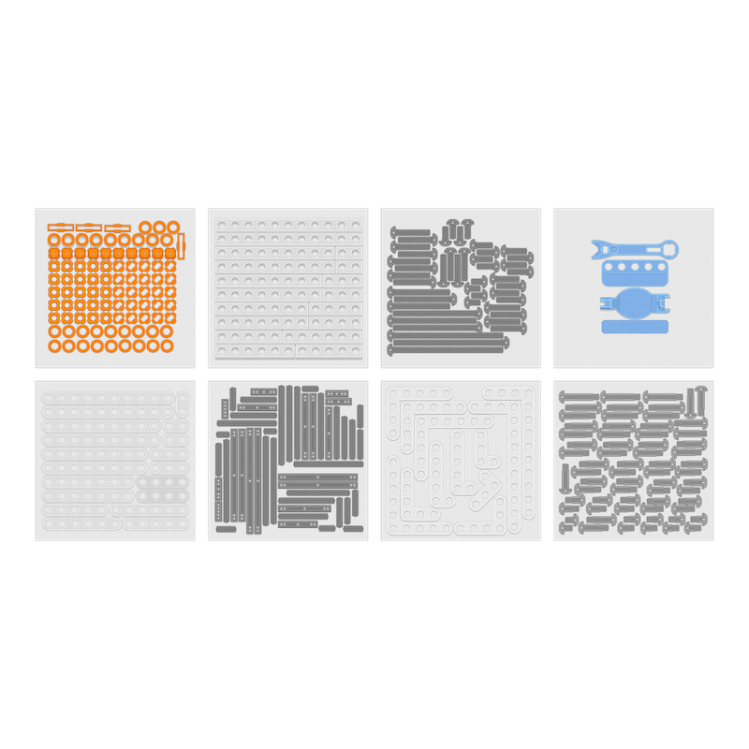
3D-printing/Build Plates/STEMFIE Essentials/STEMFIE Essentials (thumbnail).png
