Stemfie3D/STEMFIE-file-repository/3D-printing/Samples/STEMFIE.org Quick-print sample/STEMFIE.org Quick-print sample (thumbnail).png

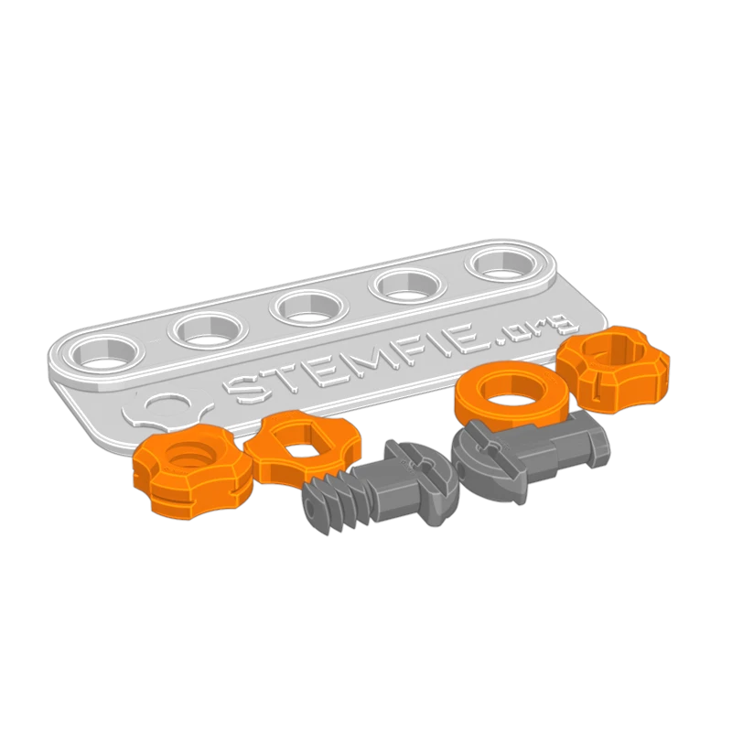
3D-printing/Samples/STEMFIE.org Quick-print sample/STEMFIE.org Quick-print sample (thumbnail).png
