Stemfie3D/STEMFIE-file-repository/Templates/STEMFIE Construction Standard/STEMFIE Construction Standard - Template - Block Unit BU01x01x01 - SCS-TPL-0001 (stemfie.org).png

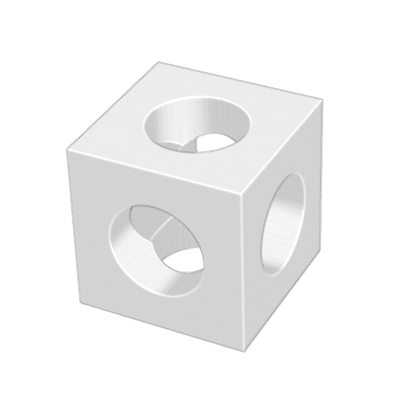
Templates/STEMFIE Construction Standard/STEMFIE Construction Standard - Template - Block Unit BU01x01x01 - SCS-TPL-0001 (stemfie.org).png
