Stemfie3D/STEMFIE-file-repository/3D-printing/Calibration/3DBenchy/3DBenchy STEMFIE.org (thumbnail).png

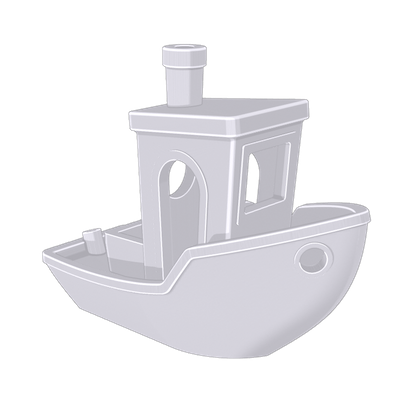
3D-printing/Calibration/3DBenchy/3DBenchy STEMFIE.org (thumbnail).png
