Stemfie3D/STEMFIE-file-repository/3D-printing/Calibration/STEMFIE Calibration File/STEMFIE Calibration File (thumbnail).png

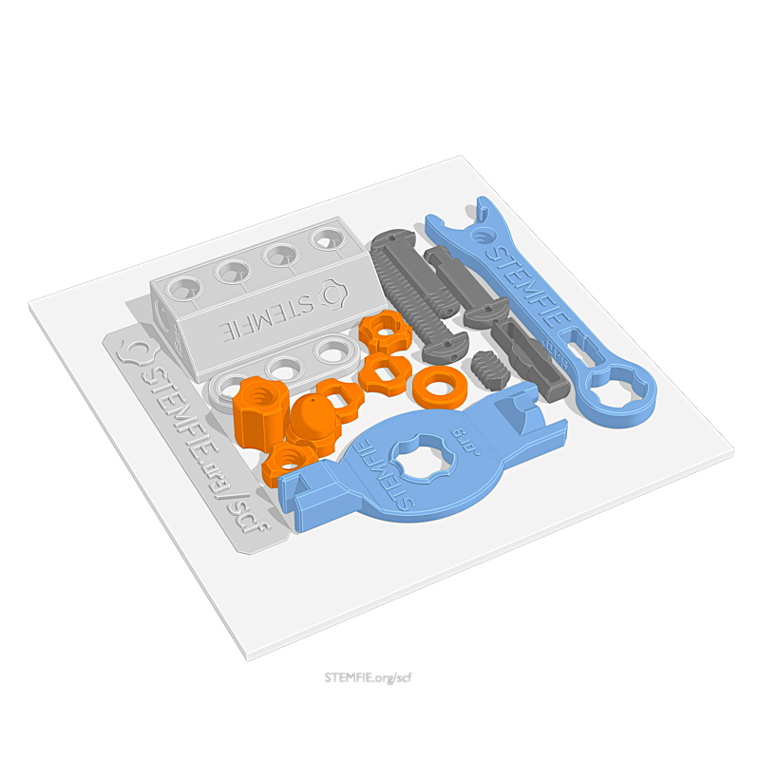
3D-printing/Calibration/STEMFIE Calibration File/STEMFIE Calibration File (thumbnail).png
